alanswx/Arcade-MCR2-TangFPGA/docs/for_mitch_2026-08-27.md

# Shield PCB — summary for Mitch, 2026-08-27

Thanks for the quick turnaround on the 08-25 review. Here is where the board
stands after your 08-27 upload (`9fb5ccc` / `22d051d`), checked the same way
as before: your committed `MCR_prototype_PCB.net` (135 parts, all 12 sheets)
now matches an independently generated netlist exactly, and both match the
`.kicad_pcb` pad-for-pad — 185 nets, zero differences. DRC is clean (0
unconnected, 0 violations). So the gerbers are the schematic; the remaining
questions are all design, not tooling.

## Fixed — thank you

| | |
|---|---|
| U1/U2 CLK ↔ LOAD swap | all six '165s consistent now |
| ESD arrays in series with caps | SRV05s on the input nodes; dropping the 32 caps is fine |
| 1N4148W feeding the console | 1N5822 on a 1.0 mm trace — good |
| decoupling | 16 × 100 nF + 2 × 100 µF; both rails covered |
| THS7374 | BYPASS on JP4, 75 Ω series on all five outputs |
| J5 | grounds on 9/18, meter across +12 V and the ULN, `Out_Clear` pulled up |

## Please fix before ordering

**1. ADS7830 logic levels (two nets).** VDD and REF are now both +5 V, which
fixes the REF-above-VDD problem but creates another: the FPGA's I²C is 3.3 V
and the ADS7830's VIH is 0.7 × VDD = 3.5 V at 5 V, so SCL/SDA highs are out
of spec. Go the other way: **VDD = +3.3 V**, leave REF as an output with
100 nF to ground (internal 2.5 V reference), and put the volume pot across
+3.3 V so the wiper stays in range.

**2. Mounting holes.** There are none — the only 3.2 mm drills are the DE-15
bracket pair, and the 1.6 mm pair is D4's leads. A 267 × 199 mm 4-layer board
with a 40-pin socket and eight MTA headers needs standoffs; four corner holes
at least.

## Worth doing on this spin (they will show up on first hookup)

**3. THS7374 input level.** The 510/1k/2k ladder still feeds the amp input
with no shunt, so full-scale is 3.3 V, doubled to 6.6 V against a ~2.3 V
linear input range — the top of the range clips. A **75 Ω to ground at each
of U13's three inputs** brings full-scale to ~0.7 V, which is what the 2×
gain and the 75 Ω series resistor are designed around. Also note the VGA
connector and J2 hang off the *same* 75 Ω, so with both plugged in the level
halves; separate resistors per connector if both stay.

**4. Audio.** The board has no amplifier. On the real cabinet, J3 pins 7/9
(and DoT's 6/7 and 9/10) are the *speaker terminals* of the sound board's own
amp — a cabinet speaker plugged into this J3 gets a 2 kΩ-source line-level
signal and will be near-silent. Either add an LM386/TPA-class stage per
channel (the spec assumed one on the 12 V rail) or document that an external
amp is required.

On the Discs of Tron 10-pin J3: per the archived pinout, 6/7 are the + and −
of speaker 1 and 9/10 of speaker 2. The board puts `AUD_PWM_R1` on 6 and
`AUD_PWM_L1` on 7 — two different channels across one speaker. DoT has two
speakers, each bridge-driven, not four. If you want the second pair
(`AUD_PWM_L2/R2` on J10 pins 1 and 5) to survive, it needs an RTL decision
on our side too — nothing generates a second stereo pair today, and those
balls currently carry video bit 0.

## Small / for the record

- No cap on the regulator side of L1/L2 (U24/U25 IN nets are just inductor +
  module pin). RECOM wants the input cap at the pin; 10 µF after each
  inductor.
- No I²C pull-ups on `ADC_SDA/SCL`. FPGA internal pull-ups will do for the
  prototype.
- `Start 1/2/3 Lamp` nets on U10 go to no connector (ERC flags them).
- J5.20/21 meter polarity is the reverse of the table (20 = Return, 21 =
  Meter 1). Harmless for a bare coil; check how the harness uses "Return".
- **J1 pin 18 = +12 V and 6/7/10/20 = GND: I could not verify these positions**
  — the archived table lists J1's functions but not its 20 pin numbers.
  Please check against the MCR power-supply manual; a wrong +12 V pin on the
  .156" connector is the one mistake that destroys parts.
- J0 (the 2×20 socket) is top-side at (125, 148). Just confirm the stacking
  and that pin 1 lands on J10 pin 1.

## Agreed / recorded on our side

- Pin 9 = service switch, pin 11 = console +5 V through D4, pins 19/20/29/30
  = ADC, pins 1/5 = second audio pair — all now in `docs/shield_j10_pinout.md`
  as built.
- RTL to-do list (I²C master, `OUT_CLEAR_N` high, second audio pair or
  retire video bit 0) is in `TODO.md` under "Shield PCB".
- Full detail with the per-item table: `docs/pcb_review_2026-08-25.md`.

---

## 2026-08-28 follow-up

Checked `d5f0787` the same way: your `.net` (143 parts), my independent
netlist and the board agree pad-for-pad (186 nets), DRC clean.

Everything I asked for is in: ADS7830 on 3.3 V with the REF cap and the pot
on 3.3 V, 1 k I²C pull-ups, 75 Ω shunts on the THS7374 inputs, 10 µF after
L1/L2, five M4 mounting holes. **From my side there is nothing left to hold
the order for.**

**Audio — you're right and I was wrong.** I had read J3's "o+/o−" as the
sound board's own speaker terminals. With the external dual-amplifier PCB
in the cabinet, line level on J3 is correct and no on-board amp is needed,
and with DoT Environmental driving four speakers independently, J3_DOT1
6/7/9/10 as four channels is the right assignment. I've withdrawn that
item. What remains from it is on our side: the FPGA doesn't generate a
second stereo pair yet, so J10 pins 1/5 will carry video bit 0 until the RTL
is updated — harmless into your RC filter.

Two small things, neither a blocker: VGA and J2 share one 75 Ω per channel,
so the level halves if both are plugged in at once; and the three start-lamp
nets on U10 still go to no connector.

The one thing I still can't check myself: **J1 pin 18 = +12 V and 6/7/10/20 =
GND** — please confirm the .156" positions against the manual before power
is applied.
