alanswx/Arcade-MCR2-TangFPGA/docs/MCR_Master_Pinouts.pdf

# Ultimate MCR Master Pinout Matrix

Connector-Pin | Standard MCR Function | Solar Fox (MCR-1) | Kick / Kickman (MCR-1) | Tron (MCR-2) | Satan's Hollow (MCR-2) | Kozmik Krooz'r (MCR-2) | Wacko (MCR-2) | Domino Man (MCR-2) | Tapper (MCR-3) | Journey (MCR-3) | Timber (MCR-3) | Discs of Tron (MCR-3) | Spy Hunter (MCR-3) | Crater Raider (MCR-3)
J2-1 | P1 Up | P1 Up | N/C | P1 Up | P1 Left | N/C | P1 Up | P1 Up | P1 Up | P1 Up | P1 Up | P1 Up | Machine Gun | N/C
J2-2 | P1 Down | P1 Down | N/C | P1 Down | P1 Right | N/C | P1 Down | P1 Down | P1 Down | P1 Down | P1 Down | P1 Down | Missiles | N/C
J2-3 | P1 Left | P1 Left | N/C | P1 Left | N/C | N/C | P1 Left | P1 Left | P1 Left | P1 Left | P1 Left | P1 Left | Oil Slick | P1 Left
J2-4 | P1 Right | P1 Right | N/C | P1 Right | N/C | N/C | P1 Right | P1 Right | P1 Right | P1 Right | P1 Right | P1 Right | Smoke Screen | P1 Right
J2-5 | P1 Button 1 | Fire / Turbo | Kick | Fire (Trigger) | Fire (Trigger) | Fire | N/C | Place / Strike | Pour / Serve | Fire | N/C | Fire (Trigger) | Weapons Van | Fire
J2-6 | P1 Button 2 | N/C | Catch | N/C | Shield | N/C | N/C | N/C | N/C | N/C | N/C | Deflect | N/C | Shield
J2-13 | Ground | Ground | Ground | Ground | Ground | Ground | Ground | Ground | Ground | Ground | Ground | Ground | Ground | Ground
J5-1 | P2 Mux / Data Bit 0 (Opt Y) | No J5 | No J5 | No J5 | No J5 | No J5 | Trackball Y-Axis (D0) | No J5 | N/C | N/C | N/C | N/C | N/C | N/C
J5-2 | P2 Mux / Data Bit 1 (Opt Y) | No J5 | No J5 | No J5 | No J5 | No J5 | Trackball Y-Axis (D1) | No J5 | N/C | N/C | N/C | N/C | N/C | N/C
J5-3 | P2 Mux / Data Bit 2 (Opt Y) | No J5 | No J5 | No J5 | No J5 | No J5 | Trackball Y-Axis (D2) | No J5 | N/C | N/C | N/C | N/C | N/C | N/C
J5-4 | P2 Mux / Data Bit 3 (Opt Y) | No J5 | No J5 | No J5 | No J5 | No J5 | Trackball Y-Axis (D3) | No J5 | N/C | N/C | N/C | N/C | N/C | N/C
J5-5 | P2 Mux / Data Bit 4 (Opt Y) | No J5 | No J5 | No J5 | No J5 | No J5 | Trackball Y-Axis (D4) | No J5 | N/C | N/C | N/C | N/C | N/C | N/C
J5-6 | P2 Mux / Data Bit 5 (Opt Y) | No J5 | No J5 | No J5 | No J5 | No J5 | Trackball Y-Axis (D5) | No J5 | N/C | N/C | N/C | N/C | N/C | N/C
J5-15 | P2 Up / Data Bit 6 (Opt Y) | No J5 | No J5 | No J5 | No J5 | No J5 | Trackball Y-Axis (D6) | No J5 | P2 Up | N/C | P2 Up | Aim Up | N/C | N/C
J5-16 | P2 Down / Data Bit 7 (Opt Y) | No J5 | No J5 | No J5 | No J5 | No J5 | Trackball Y-Axis (D7) | No J5 | P2 Down | N/C | P2 Down | Aim Down | N/C | N/C
J5-17 | P2 Left | No J5 | No J5 | No J5 | No J5 | No J5 | N/C | No J5 | P2 Left | N/C | P2 Left | N/C | N/C | N/C
J5-18 | P2 Right | No J5 | No J5 | No J5 | No J5 | No J5 | N/C | No J5 | P2 Right | N/C | P2 Right | N/C | N/C | N/C
J5-19 | P2 Button 1 | No J5 | No J5 | No J5 | No J5 | No J5 | N/C | No J5 | P2 Pour | N/C | N/C | N/C | N/C | N/C
J3-1 | Coin 1 | Coin 1 | Coin 1 | Coin 1 | Coin 1 | Coin 1 | Coin 1 | Coin 1 | Coin 1 | Coin 1 | Coin 1 | Coin 1 | Coin 1 | Coin 1
J3-2 | Coin 2 | Coin 2 | Coin 2 | Coin 2 | Coin 2 | Coin 2 | Coin 2 | Coin 2 | Coin 2 | Coin 2 | Coin 2 | Coin 2 | Coin 2 | Coin 2
J3-3 | Start 1 | Start 1 | Start 1 | Start 1 | Start 1 | Start 1 | Start 1 | Start 1 | Start 1 | Start 1 | Start 1 | Start 1 | Start 1 | Start 1
J3-4 | Start 2 | Start 2 | Start 2 | Start 2 | Start 2 | Start 2 | Start 2 | Start 2 | Start 2 | Start 2 | Start 2 | Start 2 | N/C | Start 2
J3-5 | Tilt | Tilt | Tilt | Tilt | Tilt | Tilt | Tilt | Tilt | Tilt | Tilt | Tilt | Tilt | Tilt | Tilt
J4-1 | Data Bit 0 (Opt X) | Data Bit 0 | Spinner X (D0) | Opt/Main (D0) | Data Bit 0 | Spinner X (D0) | Trackball X-Axis (D0) | Data Bit 0 | Data Bit 0 | Data Bit 0 | Data Bit 0 | Rotary (D0) | Steer/Gas (D0) | Data Bit 0
J4-2 | Data Bit 1 (Opt X) | Data Bit 1 | Spinner X (D1) | Opt/Main (D1) | Data Bit 1 | Spinner X (D1) | Trackball X-Axis (D1) | Data Bit 1 | Data Bit 1 | Data Bit 1 | Data Bit 1 | Rotary (D1) | Steer/Gas (D1) | Data Bit 1
J4-3 | Data Bit 2 (Opt X) | Data Bit 2 | Spinner X (D2) | Opt/Main (D2) | Data Bit 2 | Spinner X (D2) | Trackball X-Axis (D2) | Data Bit 2 | Data Bit 2 | Data Bit 2 | Data Bit 2 | Rotary (D2) | Steer/Gas (D2) | Data Bit 2
J4-4 | Data Bit 3 (Opt X) | Data Bit 3 | Spinner X (D3) | Opt/Main (D3) | Data Bit 3 | Spinner X (D3) | Trackball X-Axis (D3) | Data Bit 3 | Data Bit 3 | Data Bit 3 | Data Bit 3 | Rotary (D3) | Steer/Gas (D3) | Data Bit 3
J4-5 | Data Bit 4 (Opt X) | Data Bit 4 | Spinner X (D4) | Opt/Main (D4) | Data Bit 4 | Spinner X (D4) | Trackball X-Axis (D4) | Data Bit 4 | Data Bit 4 | Data Bit 4 | Data Bit 4 | Rotary (D4) | Steer/Gas (D4) | Data Bit 4
J4-6 | Data Bit 5 (Opt X) | Data Bit 5 | Spinner X (D5) | Opt/Main (D5) | Data Bit 5 | Spinner X (D5) | Trackball X-Axis (D5) | Data Bit 5 | Data Bit 5 | Data Bit 5 | Data Bit 5 | Rotary (D5) | Steer/Gas (D5) | Data Bit 5
J4-7 | Data Bit 6 (Opt X) | Data Bit 6 | Spinner X (D6) | Opt/Main (D6) | Data Bit 6 | Spinner X (D6) | Trackball X-Axis (D6) | Data Bit 6 | Data Bit 6 | Data Bit 6 | Data Bit 6 | Rotary (D6) | Steer/Gas (D6) | Data Bit 6
J4-8 | Key | Key | Key | Key | Key | Key | Key | Key | Key | Key | Key | Key | Key | Key
J4-9 | Data Bit 7 (Opt X) | Data Bit 7 | Spinner X (D7) | Opt/Main (D7) | Data Bit 7 | Spinner X (D7) | Trackball X-Axis (D7) | Data Bit 7 | Data Bit 7 | Data Bit 7 | Data Bit 7 | Rotary (D7) | Steer/Gas (D7) | Data Bit 7
J4-10 | Ground | Ground | Ground | Ground | Ground | Ground | Ground | Ground | Ground | Ground | Ground | Ground | Ground | Ground
Video - Pin 1 | Red | Red | Red | Red | Red | Red | Red | Red | Red | Red | Red | Red | Red | Red
Video - Pin 2 | Video GND | Video GND | Video GND | Video GND | Video GND | Video GND | Video GND | Video GND | Video GND | Video GND | Video GND | Video GND | Video GND | Video GND
Video - Pin 3 | Green | Green | Green | Green | Green | Green | Green | Green | Green | Green | Green | Green | Green | Green
Video - Pin 4 | Video GND | Video GND | Video GND | Video GND | Video GND | Video GND | Video GND | Video GND | Video GND | Video GND | Video GND | Video GND | Video GND | Video GND

Connector-Pin | Standard MCR Function | Solar Fox (MCR-1) | Kick / Kickman (MCR-1) | Tron (MCR-2) | Satan's Hollow (MCR-2) | Kozmik Krooz'r (MCR-2) | Wacko (MCR-2) | Domino Man (MCR-2) | Tapper (MCR-3) | Journey (MCR-3) | Timber (MCR-3) | Discs of Tron (MCR-3) | Spy Hunter (MCR-3) | Crater Raider (MCR-3)
Video - Pin 5 | Blue | Blue | Blue | Blue | Blue | Blue | Blue | Blue | Blue | Blue | Blue | Blue | Blue | Blue
Video - Pin 6 | Video GND | Video GND | Video GND | Video GND | Video GND | Video GND | Video GND | Video GND | Video GND | Video GND | Video GND | Video GND | Video GND | Video GND
Video - Pin 7 | Key | Key | Key | Key | Key | Key | Key | Key | Key | Key | Key | Key | Key | Key
Video - Pin 8 | H-Sync (-) | H-Sync (-) | H-Sync (-) | H-Sync (-) | H-Sync (-) | H-Sync (-) | H-Sync (-) | H-Sync (-) | H-Sync (-) | H-Sync (-) | H-Sync (-) | H-Sync (-) | H-Sync (-) | H-Sync (-)
Video - Pin 9 | V-Sync (-) | V-Sync (-) | V-Sync (-) | V-Sync (-) | V-Sync (-) | V-Sync (-) | V-Sync (-) | V-Sync (-) | V-Sync (-) | V-Sync (-) | V-Sync (-) | V-Sync (-) | V-Sync (-) | V-Sync (-)
