alanswx/Arcade-MCR2-TangFPGA/src/rtl/steering_control.vhd

-- Vendored 2026-07-30 from refs/Arcade-MCR3Scroll_MiSTer/rtl/steering_control.vhd
-- (MiSTer Arcade-MCR3Scroll). Unmodified. Absolute-position wheel/pedal
-- decoder simulation for Spy Hunter and Turbo Tag; lives in the TOP, not the
-- core, exactly as upstream has it.
library ieee;
use ieee.std_logic_1164.all;
use ieee.std_logic_unsigned.all;
use ieee.numeric_std.all;

entity steering_control is
generic (
	steering_min   : std_logic_vector(7 downto 0) := x"34";
	steering_max   : std_logic_vector(7 downto 0) := x"B4";
	steering_mid   : std_logic_vector(7 downto 0) := x"74";
	steering_step  : std_logic_vector(7 downto 0) := x"08";
	gas_min        : std_logic_vector(8 downto 0) := '0'&x"30";
	gas_max        : std_logic_vector(8 downto 0) := '0'&x"FF";
	gas_step       : std_logic_vector(8 downto 0) := '0'&x"08";
	gas_reverse    : std_logic := '0'
);
port(
	clk            : in  std_logic;
	reset          : in  std_logic;
	vsync          : in  std_logic;

	gas_plus       : in  std_logic;
	gas_minus      : in  std_logic;
	steering_plus  : in  std_logic;
	steering_minus : in  std_logic;
	steering       : out std_logic_vector(7 downto 0);
	gas            : out std_logic_vector(7 downto 0)
);
end steering_control;

architecture struct of steering_control is
	signal steering_r       : std_logic_vector(7 downto 0);
	signal steering_next    : std_logic_vector(7 downto 0);
	signal steering_plus_r  : std_logic;
	signal steering_minus_r : std_logic;
	signal steering_timer   : std_logic_vector(5 downto 0);

	signal gas_r            : std_logic_vector(8 downto 0);
	signal gas_next         : std_logic_vector(8 downto 0);
	signal gas_plus_r       : std_logic;
	signal gas_minus_r      : std_logic;
	signal gas_timer        : std_logic_vector(5 downto 0);

	signal vsync_r          : std_logic;
begin

-- absolute position decoder simulation
--
--  steering :
--       thresholds        median
--   F5 <  left 8   < 34    30
--   35 <  left 7   < 3C    38
--   3D <  left 6   < 44    40
--   45 <  left 5   < 4C    48     
--   4D <  left 4   < 54    50
--   45 <  left 3   < 5C    58
--   5D <  left 2   < 64    60
--   65 <  left 1   < 6C    68
--   6D < centrered < 74    70
--   75 <  right 1  < 7C    78
--   7D <  right 2  < 84    80
--   85 <  right 3  < 8C    88
--   8D <  right 4  < 94    90
--   95 <  right 5  < 9C    98
--   9D <  right 6  < A4    A0
--   A5 <  right 7  < AC    A8
--   AD <  right 8  < F4    BO

-- gas :
--         threshold          median
--    00 < gas pedal 00 < 3B   (39)  3E-5
--    3C < gas pedal 01 < 40    3E
--    41 < gas pedal 02 < 45    43
--    46 < gas pedal 03 < 4A    48      
--    4B < gas pedal 04 < 4F    4D
--    50 < gas pedal 05 < 54    52
--    55 < gas pedal 06 < 59    57
--    5A < gas pedal 07 < 5E    5C
--    5F < gas pedal 08 < 63    61
--     ...
--    FA < gas pedal 27 < FE    FC
--    FF = gas pedal 28        (FF)  FC+4


gas <= gas_r(7 downto 0);
gas_next <= gas_r - gas_step when gas_plus  = '1' and gas_reverse = '1' else
            gas_r + gas_step when gas_minus = '1' and gas_reverse = '1' else
            gas_r + gas_step when gas_plus  = '1' and gas_reverse = '0' else
            gas_r - gas_step when gas_minus = '1' and gas_reverse = '0' else
            gas_r;

steering <= steering_r;
steering_next <= steering_r + steering_step when steering_plus = '1' else steering_r - steering_step;

process (clk, reset)
begin
	if reset = '1' then
		if gas_reverse = '1' then
			gas_r <= gas_max;
		else
			gas_r <= gas_min;
		end if;
		steering_r <= steering_mid;
	else

		if rising_edge(clk) then
			gas_plus_r       <= gas_plus;
			gas_minus_r      <= gas_minus;
			steering_plus_r  <= steering_plus;
			steering_minus_r <= steering_minus;
			vsync_r          <= vsync;
			
			-- gas increase/decrease as long as btn is pushed
			-- keep current value when no btn is pushed
			if (gas_plus_r = not gas_plus)  or (gas_minus_r = not gas_minus) then
				gas_timer <= (others => '0');
			else
				if vsync_r ='0' and vsync = '1' then 
					if (gas_timer >= 5 and (gas_minus_r = '1' or gas_plus_r = '1')) then --tune inc/dec rate
						gas_timer <= (others => '0');
					else
						gas_timer <= gas_timer + 1;
					end if;
				end if;
			end if;

			if vsync_r ='0' and vsync = '1' and gas_timer = 0 then	
				gas_r <= gas_next;
				if gas_next < gas_min then
					gas_r <= gas_min;
				elsif gas_next > gas_max then
					gas_r <= gas_max;
				end if;
			end if;

			-- steering increase/decrease as long as btn is pushed
			-- return to center value when no btn is pushed
			if (steering_plus_r = not steering_plus)  or (steering_minus_r = not steering_minus) then
				steering_timer <= (others => '0');
			else
				if vsync_r ='0' and vsync = '1' then 
					if (steering_timer >= 7 and (steering_minus_r = '1' or  steering_plus_r = '1')) or   -- tune btn pushed   rate
						(steering_timer >= 3 and (steering_minus_r = '0' and steering_plus_r = '0')) then -- tune btn released rate
						steering_timer <= (others => '0');
					else
						steering_timer <= steering_timer + 1;
					end if;
				end if;
			end if;
			
			if vsync_r ='0' and vsync = '1' and steering_timer = 0 then	
				if steering_plus = '1' then 
					if steering_next > steering_max then steering_r <= steering_max; else steering_r <= steering_next; end if;
				elsif steering_minus = '1' then
					if steering_next < steering_min then steering_r <= steering_min; else steering_r <= steering_next; end if;
				else
					if steering_r < steering_mid - steering_step then steering_r <= steering_r + steering_step; end if;						
					if steering_r > steering_mid + steering_step then steering_r <= steering_r - steering_step; end if;
					if (steering_r >= steering_mid - steering_step) and (steering_r <= steering_mid + steering_step) then steering_r <= steering_mid; end if;						
				end if;
			end if;
		end if;
	end if;
end process;	

end struct;
