alanswx/Arcade-MCR2-TangFPGA/src/rtl/sdram_gw.sv

// sdram_gw.sv - Gowin adaptation of the MiSTer Arcade-MCR3 multi-port
// SDRAM controller (refs/Arcade-MCR3_MiSTer/rtl/sdram.sv), vendored 2026-07.
// Only change from upstream: module renamed and the Altera altddio_out
// SDRAM_CLK forwarder replaced with a Gowin ODDR (see below). This is the
// controller MCR-3 will use; the SDRAM memtest exercises it so the physical
// module + pins + clock phase are validated before a core rides on it.
// Runs at ~100 MHz (refresh RFRSH_CYCLES sized for that).
//
// sdram.v
//
// sdram controller implementation for the MiST board
// https://github.com/mist-devel/mist-board
// 
// Copyright (c) 2013 Till Harbaum <till@harbaum.org> 
// Copyright (c) 2019 Gyorgy Szombathelyi
//
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

module sdram_gw #(
	// Cycles between auto-refreshes. Default 842 suits the memtest's 100 MHz
	// clock; the MCR-3 build runs at 80 MHz and overrides to 600 (7.5us < the
	// 7.81us tREF row interval). Sized per SDRAM clock so data is retained.
	parameter [9:0] RFRSH_CYCLES = 10'd842,
	// RAS-only refresh (2026-07-24): measured on the Tang SDRAM module, the
	// array decays to all-FF in ~26s with NO access while AUTO_REFRESH issues
	// at the correct ~133k/s - commands sent but ineffective. AUTO_REFRESH is
	// the only command asserting nRAS and nCAS low together; reads/writes
	// (proven-good patterns) never do. This mode refreshes via explicit
	// ACTIVE(bank,row) + PRECHARGE-ALL instead. Needs 4x the command rate
	// (per-bank rows): set RFRSH_CYCLES ~150 at 80MHz.
	parameter       RAS_REFRESH  = 1'b0
) (

	// interface to the MT48LC16M16 chip
	inout      [15:0] SDRAM_DQ,   // 16 bit bidirectional data bus (Gowin: driven via the tristate assign below)
	output reg [12:0] SDRAM_A,    // 13 bit multiplexed address bus
	output            SDRAM_DQML, // two byte masks (continuously assigned)
	output            SDRAM_DQMH, // two byte masks
	output reg [1:0]  SDRAM_BA,   // two banks
	output            SDRAM_nCS,  // a single chip select
	output            SDRAM_nWE,  // write enable
	output            SDRAM_nRAS, // row address select
	output            SDRAM_nCAS, // columns address select
	output            SDRAM_CKE,
	output            SDRAM_CLK, 
	
	// cpu/chipset interface
	input             init_n,     // init signal after FPGA config to initialize RAM
	input             clk,        // sdram clock
	// Optional phase-shifted copy of clk for the SDRAM_CLK pin forwarder
	// (see the ODDR at the bottom). Tie to clk when no shift is wanted.
	input             clk_fwd,

	input             port1_req,
	output reg        port1_ack,
	input             port1_we,
	input      [23:1] port1_a,
	input       [1:0] port1_ds,
	input      [15:0] port1_d,
	output reg [15:0] port1_q,

	input      [23:1] cpu1_addr,
	output reg [15:0] cpu1_q,
	input      [23:1] cpu2_addr,
	output reg [15:0] cpu2_q,
	input      [23:1] cpu3_addr,
	output reg [15:0] cpu3_q,

	input             port2_req,
	output reg        port2_ack,
	input             port2_we,
	input      [23:1] port2_a,
	input       [1:0] port2_ds,
	input      [15:0] port2_d,
	output reg [31:0] port2_q,
	
	input      [23:2] sp_addr,
	output reg [31:0] sp_q,

	// DIAGNOSTIC (temporary): counts AUTO_REFRESH commands actually issued.
	// At 80 MHz / RFRSH_CYCLES=600 expect ~133k/s (wraps ~3x/s). Frozen at 0
	// means the refresh branch never fires. Leave unconnected when unused.
	// 24-bit: at the intended ~133k/s a 16-bit counter wraps ~4x between
	// beacon samples, which made the rate unmeasurable (and produced the
	// bogus "2.3k/s starvation" reading). The top displays bits [23:8].
	output reg [23:0] dbg_refresh = 24'd0,
	// DIAGNOSTIC: refresh-demand cycles lost to each blocker (RAS1 slots where
	// need_refresh was pending): blk1 = bank2/3 port busy, blk0 = port[0]
	// we/oe_latch gate. Whichever runs ~130k/s is what starves refresh.
	output reg [15:0] dbg_blk0 = 16'd0,
	output reg [15:0] dbg_blk1 = 16'd0
);

assign SDRAM_CKE = 1;
assign SDRAM_nCS = 0;
assign { SDRAM_DQMH, SDRAM_DQML } = SDRAM_A[12:11];

// Gowin bidirectional DQ: MiSTer drove `inout reg SDRAM_DQ` procedurally,
// which Gowin rejects (EX3900). Model the tristate explicitly instead.
reg  [15:0] sd_dq_out;
reg         sd_dq_oe;
assign SDRAM_DQ = sd_dq_oe ? sd_dq_out : 16'bZ;

localparam RASCAS_DELAY   = 3'd2;   // tRCD=20ns -> 2 cycles@<100MHz
localparam BURST_LENGTH   = 3'b001; // 000=1, 001=2, 010=4, 011=8
localparam ACCESS_TYPE    = 1'b0;   // 0=sequential, 1=interleaved
localparam CAS_LATENCY    = 3'd2;   // CL2, as nand2mario runs this module
localparam OP_MODE        = 2'b00;  // only 00 (standard operation) allowed
localparam NO_WRITE_BURST = 1'b1;   // 0= write burst enabled, 1=only single access write

localparam MODE = { 3'b000, NO_WRITE_BURST, OP_MODE, CAS_LATENCY, ACCESS_TYPE, BURST_LENGTH}; 

// 64ms/8192 rows = 7.8us -> 842 cycles@108MHz
// RFRSH_CYCLES is now a module parameter (see the header) so the 80 MHz MCR-3
// build can shrink it; the memtest leaves it at the 842 default.

// ---------------------------------------------------------------------
// ------------------------ cycle state machine ------------------------
// ---------------------------------------------------------------------

/*
 SDRAM state machine for 2 bank interleaved access
 1 word burst, CL2
cmd issued  registered
 0 RAS0     
 1          ras0, data1 returned
 2 CAS0     data1 returned
 3 RAS1     cas0
 4          ras1
 5 CAS1     data0 returned
 6          cas1, data0 returned (discarded)
 
*/

localparam STATE_FIRST     = 3'd0;   // first state in cycle
localparam STATE_RAS0      = 3'd0;
localparam STATE_RAS1      = 3'd3;   // Second ACTIVE command after RAS0 + tRRD (15ns)
localparam STATE_CAS0      = STATE_RAS0 + RASCAS_DELAY; // CAS phase - 2
localparam STATE_CAS1      = STATE_RAS1 + RASCAS_DELAY; // CAS phase - 5
localparam STATE_READ1     = 3'd2;   // upstream value (moving these past
localparam STATE_READ1b    = 3'd3;   // RAS1 breaks oe_latch clearing - use
                                     // CAP_DELAY on the data path instead)
localparam STATE_READ0     = 3'd6;
localparam STATE_LAST      = 3'd6;

reg [2:0] t;
always @(posedge clk) begin
	t <= t + 1'd1;
	if (t == STATE_LAST) t <= STATE_FIRST;
end

// ---------------------------------------------------------------------
// --------------------------- startup/reset ---------------------------
// ---------------------------------------------------------------------

// wait 1ms (32 8Mhz cycles) after FPGA config is done before going
// into normal operation. Initialize the ram in the last 16 reset cycles (cycles 15-0)
reg [4:0]  reset;
reg        init = 1'b1;
always @(posedge clk, negedge init_n) begin
	if(!init_n) begin
		reset <= 5'h1f;
		init <= 1'b1;
	end else begin
		if((t == STATE_LAST) && (reset != 0)) reset <= reset - 5'd1;
		init <= !(reset == 0);
	end
end

// ---------------------------------------------------------------------
// ------------------ generate ram control signals ---------------------
// ---------------------------------------------------------------------

// all possible commands
localparam CMD_NOP             = 3'b111;
localparam CMD_ACTIVE          = 3'b011;
localparam CMD_READ            = 3'b101;
localparam CMD_WRITE           = 3'b100;
localparam CMD_BURST_TERMINATE = 3'b110;
localparam CMD_PRECHARGE       = 3'b010;
localparam CMD_AUTO_REFRESH    = 3'b001;
localparam CMD_LOAD_MODE       = 3'b000;

reg [2:0]  sd_cmd;   // current command sent to sd ram
reg [15:0] sd_din;
reg [15:0] sp_q_lo;  // first burst beat of an sp read, committed at READ1b
// drive control signals according to current command
assign SDRAM_nRAS = sd_cmd[2];
assign SDRAM_nCAS = sd_cmd[1];
assign SDRAM_nWE  = sd_cmd[0];

reg [23:1] addr_latch[3];
reg [23:1] addr_latch_next[2];
reg [23:1] addr_last[4];
reg [23:2] addr_last2[2];
reg [15:0] din_latch[2];
reg  [1:0] oe_latch;
reg  [1:0] we_latch;
reg  [1:0] ds[2];

reg        port1_state;
reg        port2_state;

localparam PORT_NONE  = 3'd0;
localparam PORT_CPU1  = 3'd1;
localparam PORT_CPU2  = 3'd2;
localparam PORT_CPU3  = 3'd3;
localparam PORT_SP    = 3'd1;
localparam PORT_REQ   = 3'd4;

reg  [2:0] next_port[2];
reg  [2:0] port[2];

reg        refresh;
reg [10:0] refresh_cnt;
reg        need_refresh;
reg [14:0] ref_cnt   = 15'd0;   // RAS_REFRESH: {row[12:0], bank[1:0]}
reg        ref_phase = 1'b0;    // RAS_REFRESH: row open, precharge next slot

// PORT1: bank 0,1
always @(*) begin
	if (refresh) begin
		next_port[0] = PORT_NONE;
		addr_latch_next[0] = addr_latch[0];
	end else if (port1_req ^ port1_state) begin
		next_port[0] = PORT_REQ;
		addr_latch_next[0] = port1_a;
	end else if (cpu1_addr != addr_last[PORT_CPU1]) begin
		next_port[0] = PORT_CPU1;
		addr_latch_next[0] = cpu1_addr;
	end else if (cpu2_addr != addr_last[PORT_CPU2]) begin
		next_port[0] = PORT_CPU2;
		addr_latch_next[0] = cpu2_addr;
	end else if (cpu3_addr != addr_last[PORT_CPU3]) begin
		next_port[0] = PORT_CPU3;
		addr_latch_next[0] = cpu3_addr;
	end else begin
		next_port[0] = PORT_NONE;
		addr_latch_next[0] = addr_latch[0];
	end
end

// PORT1: bank 2,3
always @(*) begin
	if (port2_req ^ port2_state) begin
		next_port[1] = PORT_REQ;
		addr_latch_next[1] = port2_a;
	end else if (sp_addr != addr_last2[PORT_SP]) begin
		next_port[1] = PORT_SP;
		addr_latch_next[1] = { sp_addr, 1'b0 };
	end else begin
		next_port[1] = PORT_NONE;
		addr_latch_next[1] = addr_latch[1];
	end
end

always @(posedge clk) begin

	// permanently latch ram data to reduce delays
	sd_din <= SDRAM_DQ;
	sd_dq_oe <= 1'b0;   // release the bus (Gowin tristate)
	sd_cmd <= CMD_NOP;  // default: idle
	if(~&refresh_cnt) refresh_cnt <= refresh_cnt + 1'd1;
	need_refresh <= (refresh_cnt >= RFRSH_CYCLES);

	if(init) begin
		// initialization takes place at the end of the reset phase
		if(t == STATE_FIRST) begin

			if(reset == 15) begin
				sd_cmd <= CMD_PRECHARGE;
				SDRAM_A[10] <= 1'b1;      // precharge all banks
			end

			if(reset == 10 || reset == 8) begin
				sd_cmd <= CMD_AUTO_REFRESH;
			end

			if(reset == 2) begin
				sd_cmd <= CMD_LOAD_MODE;
				SDRAM_A <= MODE;
				SDRAM_BA <= 2'b00;
			end
		end
	end else begin
		// RAS phase
		// bank 0,1
		if(t == STATE_RAS0) begin
			addr_latch[0] <= addr_latch_next[0];
			port[0] <= next_port[0];
			{ oe_latch[0], we_latch[0] } <= 2'b00;

			if (next_port[0] != PORT_NONE) begin
				sd_cmd <= CMD_ACTIVE;
				SDRAM_A <= addr_latch_next[0][22:10];
				SDRAM_BA <= {1'b0, addr_latch_next[0][23]};
				addr_last[next_port[0]] <= addr_latch_next[0];
				if (next_port[0] == PORT_REQ) begin
					{ oe_latch[0], we_latch[0] } <= { ~port1_we, port1_we };
					ds[0] <= port1_ds;
					din_latch[0] <= port1_d;
					port1_state <= port1_req;
				end else begin
					{ oe_latch[0], we_latch[0] } <= 2'b10;
					ds[0] <= 2'b11;
				end
			end
		end

		// bank 2,3
		if(t == STATE_RAS1) begin
			refresh <= 1'b0;
			addr_latch[1] <= addr_latch_next[1];
			{ oe_latch[1], we_latch[1] } <= 2'b00;
			port[1] <= next_port[1];

			if (RAS_REFRESH && ref_phase) begin
				// close the refresh row opened last frame (RAS1->RAS1 = 7 cycles
				// = 87.5ns >= tRAS). Nothing else is open: port0 idle, port1/2
				// bursts auto-precharge. Pending port work waits one frame.
				sd_cmd <= CMD_PRECHARGE;
				SDRAM_A[10] <= 1'b1;
				ref_phase <= 1'b0;
				port[1] <= PORT_NONE;   // don't launch work this slot
			end
			else if (next_port[1] != PORT_NONE) begin
				if (need_refresh) dbg_blk1 <= dbg_blk1 + 1'd1;
				sd_cmd <= CMD_ACTIVE;
				SDRAM_A <= addr_latch_next[1][22:10];
				SDRAM_BA <= {1'b1, addr_latch_next[1][23]};
				addr_last2[next_port[1]] <= addr_latch_next[1][23:2];
				if (next_port[1] == PORT_REQ) begin
					// NOTE: this is the port2 (bank 2,3) path - it must gate on
					// port2_we, not port1_we. The original had port1_we here (a
					// copy-paste from the bank 0,1 block); harmless until port2
					// is actually used for writes (MCR-3 sprite load), where it
					// made every port2 write silently decode as a read.
					{ oe_latch[1], we_latch[1] } <= { ~port2_we, port2_we };
					ds[1] <= port2_ds;
					din_latch[1] <= port2_d;
					port2_state <= port2_req;
				end else begin
					{ oe_latch[1], we_latch[1] } <= 2'b10;
					ds[1] <= 2'b11;
				end
			end
			else if (need_refresh && !we_latch[0] && !oe_latch[0]) begin
				refresh <= 1'b1;
				refresh_cnt <= 0;
				dbg_refresh <= dbg_refresh + 1'd1;
				if (RAS_REFRESH) begin
					sd_cmd    <= CMD_ACTIVE;
					SDRAM_BA  <= ref_cnt[1:0];
					SDRAM_A   <= ref_cnt[14:2];
					ref_cnt   <= ref_cnt + 15'd1;
					ref_phase <= 1'b1;
				end else begin
					sd_cmd <= CMD_AUTO_REFRESH;
				end
			end
			else if (need_refresh) begin
				dbg_blk0 <= dbg_blk0 + 1'd1;
			end
		end

		// CAS phase
		if(t == STATE_CAS0 && (we_latch[0] || oe_latch[0])) begin
			sd_cmd <= we_latch[0]?CMD_WRITE:CMD_READ;
			SDRAM_A <= { 4'b0010, addr_latch[0][9:1] };  // auto precharge
			SDRAM_BA <= {1'b0, addr_latch[0][23]};
			if (we_latch[0]) begin
				SDRAM_A[12:11] <= ~ds[0];
				sd_dq_out <= din_latch[0]; sd_dq_oe <= 1'b1;
				port1_ack <= port1_req;
			end
		end

		if(t == STATE_CAS1 && (we_latch[1] || oe_latch[1])) begin
			sd_cmd <= we_latch[1]?CMD_WRITE:CMD_READ;
			SDRAM_A <= { 4'b0010, addr_latch[1][9:1] };  // auto precharge
			SDRAM_BA <= {1'b1, addr_latch[1][23]};
			if (we_latch[1]) begin
				SDRAM_A[12:11] <= ~ds[1];
				sd_dq_out <= din_latch[1]; sd_dq_oe <= 1'b1;
				port2_ack <= port2_req;
			end
		end

		// Data returned
		if(t == STATE_READ0 && oe_latch[0]) begin
			case(port[0])
				PORT_REQ:  begin port1_q <= sd_din; port1_ack <= port1_req; end
				PORT_CPU1: begin cpu1_q  <= sd_din; end
				PORT_CPU2: begin cpu2_q  <= sd_din; end
				PORT_CPU3: begin cpu3_q  <= sd_din; end
				default: ;
			endcase;
		end

		// sp has no ack handshake, so its consumer (a slower synchronous
		// clock) can sample sp_q on ANY cycle - including between the two
		// burst beats. Upstream wrote sp_q[15:0] here and [31:16] one cycle
		// later at READ1b, leaving a window where sp_q is half new word,
		// half stale. Buffer the first beat and commit all 32 bits in one
		// cycle at READ1b instead. (port2_q keeps the two-stage update: its
		// consumers wait for port2_ack, which rises with the second beat.)
		if(t == STATE_READ1 && oe_latch[1]) begin
			case(port[1])
				PORT_REQ:	port2_q[15:0] <= sd_din;
				PORT_SP :    sp_q_lo <= sd_din;
				default: ;
			endcase;
		end

		if(t == STATE_READ1b && oe_latch[1]) begin
			case(port[1])
				PORT_REQ: begin port2_q[31:16] <= sd_din; port2_ack <= port2_req; end
				PORT_SP : begin    sp_q <= { sd_din, sp_q_lo }; end
				default: ;
			endcase;
		end
	end
end

// SDRAM_CLK forwarded through a Gowin ODDR (was Altera altddio_out).
// PHASE (the one bring-up knob): D0=1/D1=0 -> pin follows clk (0 deg fwd).
// The initial D0=0/D1=1 (180 deg) failed on hardware - the memtest reported
// the module responding but returning wrong read data (c0, got != expected),
// the textbook wrong-phase symptom - so this is flipped to 0 deg.
ODDR sdramclk_ddr (
	.Q0(SDRAM_CLK),
	.Q1(),
	.D0(1'b1),
	.D1(1'b0),
	.TX(1'b0),
	.CLK(clk_fwd)
);

endmodule
