alanswx/Arcade-MCR2-TangFPGA/src/rtl/mcr3scroll.vhd

---------------------------------------------------------------------------------
-- MCR3Scroll by Dar (darfpga@aol.fr) (06/12/2019)
-- http://darfpga.blogspot.fr
---------------------------------------------------------------------------------
--
-- release rev 00 : initial release
--  (06/12/2019)
--
---------------------------------------------------------------------------------
-- gen_ram.vhd & io_ps2_keyboard
-------------------------------- 
-- Copyright 2005-2008 by Peter Wendrich (pwsoft@syntiac.com)
-- http://www.syntiac.com/fpga64.html
---------------------------------------------------------------------------------
-- T80/T80se - Version : 304
-----------------------------
-- Z80 compatible microprocessor core
-- Copyright (c) 2001-2002 Daniel Wallner (jesus@opencores.org)
---------------------------------------------------------------------------------
-- YM2149 (AY-3-8910)
-- Copyright (c) MikeJ - Jan 2005
---------------------------------------------------------------------------------
-- Educational use only
-- Do not redistribute synthetized file with roms
-- Do not redistribute roms whatever the form
-- Use at your own risk
---------------------------------------------------------------------------------

--  Features :
--   Video        : VGA 31Khz/60Hz progressive and TV 15kHz interlaced
--   Coctail mode : NO
--   Sound        : OK - missing cheap/chip squeak deluxe board

--  MCR3Scroll (midway mcr) Hardware caracteristics :
--
--  VIDEO : 1xZ80@3MHz CPU accessing its program rom, working ram,
--    sprite data ram, I/O, sound board register and trigger.
--		  56Kx8bits program rom
--
--    One char tile map 30x32 tiles of 8x8 pixels 
--      1x4Kx8bits graphics rom 2bits/pixel single hard wired color set 

--    One scroling background tile map 16x64 tile of 8x32 pixels
--      2x16Kx8bits graphics rom 4bits/pixel single color set
--      rbg programmable ram palette 64 (16 for background) colors 9bits : 3red 3green 3blue
--
--    128 sprites, up to ~30/line, 32x32 with flip H/V
--      4x32Kx8bits graphics rom 4bits/pixel single color set
--      rbg programmable ram palette 64 (16 for sprites) colors 9bits : 3red 3green 3blue 
--
--    Working ram : 2Kx8bits
--    video char ram  : 1Kx8bits
--    video background ram  : 2Kx8bits
--    Sprites ram : 512x8bits + 512x8bits cache buffer

--    Sprites line buffer rams (graphics and colors) : 1 scan line delay flip/flop 2x256x8bits
--
--  SOUND : see tron_sound_board.vhd

---------------------------------------------------------------------------------
--  Schematics remarks :
--
--		Display is 512x480 pixels  (video 635x525 lines @ 20MHz )

--       635/20e6  = 31.75us per line  (31.750KHz)
--       31.75*525 = 16.67ms per frame (59.99Hz)
--        
--    Original video is interlaced 240 display lines per 1/2 frame
--
--       H0 and V0 are not use for background => each bg tile is 16x16 pixel but 
--			background graphics is 2x2 pixels defintion.
--
--			Sprite are 32x32 pixels with 1x1 pixel definition, 16 lines for odd 1/2
--       frame and 16 lines for even 2/2 frame thanks to V8 on sprite rom ROMAD2
--       (look at 74ls86 G1 pin 9 on video genration board schematics)
--
--    *H and V stand for Horizontal en Vertical counter (Hcnt, Vcnt in VHDL code)
--
--    /!\ For VHDL port interlaced video mode is replaced with progressive video 
--        mode.
--
--    Real hardware uses background ram access after each 1/2 frame (~line 240
--    and 480). In these areas cpu can access ram since scanlines are out of
--    visible display. In progessive mode there are video access around lines 240.
--    These accesses will create video artfacts aound mid display. In VHDL code
--    ram access is muliplexed between cpu and scanlines by using hcnt(0) in
--    order to avoid these artefacts.
--
--    Sprite data are stored first by cpu into a 'cache' buffer (staging ram at
--    K6/L6) this buffer is read and write for cpu. After visible display, cache
--    buffer (512x8) is moved to actual sprite ram buffer (512x8). Actual sprite
--    buffer is access by transfer address counter during 2 scanlines after 
--    visible area and only by sprite machine during visible area.
--
--    Thus cpu can read and update sprites position during entire frame except
--    during 2 lines.
-- 
--    Sprite data are organised (as seen by cpu F000-F1FF) into 128 * 4bytes.
--    bytes #1 : Vertical position
--    bytes #2 : code and attribute
--    bytes #3 : Horizontal position
--    bytes #4 : not used
--
--		Athough 1x1 pixel defintion sprite position horizontal/vertical is made on
--    on a 2x2 grid (due to only 8bits for position data)
--
--    Z80-CTC : interruption ar managed by CTC chip. ONly channel 3 is trigered
--    by hardware signal line 493. channel 0 to 2 are in timer mode. Schematic 
--    show zc/to of channel 0 connected to clk/trg of channel 1. This seems to be
--    unsued for that (Kick) game. 
--
--    Z80-CTC VHDL port keep separated interrupt controler and each counter so 
--    one can use them on its own. Priority daisy-chain is not done (not used in
--    that game). clock polarity selection is not done since it has no meaning
--    with digital clock/enable (e.g cpu_ena signal) method.
--
--    Ressource : input clock 40MHz is chosen to allow easy making of 20MHz for
--    pixel clock and 8MHz signal for amplitude modulation circuit of ssio board
--
--  TODO :
--    Working ram could be initialized to set initial difficulty level and
--    initial bases (live) number. Otherwise one can set it up by using service
--    menu at each power up.
--
---------------------------------------------------------------------------------

library ieee;
use ieee.std_logic_1164.all;
use ieee.std_logic_unsigned.all;
use ieee.numeric_std.all;

entity mcr3scroll is
-- Graphics-ROM baking and the CSD sound board, per board (2026-07-30). Same
-- discipline as mcr2.vhd/mcr1.vhd: defaults bake so a future standalone
-- MCR3Scroll board keeps working, while the merged 60K top passes an empty
-- name + GFX_LOADABLE => 1 so the bitstream carries NO ROM data (licensing,
-- TODO item 2). dpram needs LOADABLE whenever INIT_FILE is empty or its port B
-- silently goes read-only and the download dies with no error anywhere.
-- CSD_ENABLE => 0 removes the Cheap Squeak Deluxe board (68000 + PIA) for
-- Crater Raider, which is SSIO-only; Spy Hunter and Turbo Tag need it.
generic(
 -- bg gfx generics are absent by design: those RAMs are HOISTED to the top
 -- (see bg_addr/bg1_do/bg2_do below). Only the CHAR plane is still inside.
 CH_INIT      : string  := "rom_gfx_ch.hex";
 GFX_LOADABLE : integer := 0;
 CSD_ENABLE   : integer := 1;
 -- Sprite line buffers: 256x8 each, so an 18 Kb BSRAM block per buffer is
 -- almost entirely wasted. SPRLINE_RAMSTYLE lets a board move them to LUT RAM
 -- instead; the merged 3-family build has TEN across its cores and needs the
 -- blocks. Default "block_ram" keeps every existing board bit-identical.
 SPRLINE_RAMSTYLE : string := "block_ram";
 -- See the scratch-RAM ports below.
 SCRATCH_EXTERNAL : integer := 0;
 -- video_ram is split out so a board can hoist the small scratch RAMs but let
 -- a core keep its OWN video RAM. The merged build does that for MCR-3: at
 -- four cores the 4:1 mux on this RAM's CPU-side address sat on the critical
 -- path, and one BSRAM block buys the margin back.
 VRAM_EXTERNAL    : integer := 0
);
port(
  clock_40       : in  std_logic;
  reset          : in  std_logic;
  tv15Khz_mode   : in  std_logic;
  video_r        : out std_logic_vector(2 downto 0);
  video_g        : out std_logic_vector(2 downto 0);
  video_b        : out std_logic_vector(2 downto 0);
  video_csync    : out std_logic;
  video_hblank   : out std_logic;
  video_Vblank   : out std_logic;
  video_hs       : out std_logic;
  video_vs       : out std_logic;
  video_ce       : out std_logic;
  -- Local addition (matches src/rtl/mcr2.vhd / mcr1.vhd): expose the raster
  -- counter so the Tang top can align the framebuffer capture window; the
  -- video scanner is the same 633-wrap design as the other cores.
  hcnt_out       : out std_logic_vector(9 downto 0);
  vcnt_out       : out std_logic_vector(9 downto 0);
  cpu_halt_n     : out std_logic;   -- T80 HALT export (boot wedge watchdog)

  mod_crater     : in  std_logic;
  mod_turbo      : in  std_logic;

  separate_audio : in  std_logic;
  audio_out_l    : out std_logic_vector(15 downto 0);
  audio_out_r    : out std_logic_vector(15 downto 0);
  csd_audio_out  : out std_logic_vector( 9 downto 0);

  input_0        : in  std_logic_vector( 7 downto 0);
  input_1        : in  std_logic_vector( 7 downto 0);
  input_2        : in  std_logic_vector( 7 downto 0);
  input_3        : in  std_logic_vector( 7 downto 0);
  input_4        : in  std_logic_vector( 7 downto 0);
  output_4       : out std_logic_vector(7 downto 0);
  show_lamps     : in  std_logic; 
  
  cpu_rom_addr   : out std_logic_vector(15 downto 0);
  cpu_rom_do     : in  std_logic_vector( 7 downto 0);
  snd_rom_addr   : out std_logic_vector(13 downto 0);
  snd_rom_do     : in  std_logic_vector( 7 downto 0);
  csd_rom_addr   : out std_logic_vector(14 downto 1);
  csd_rom_do     : in  std_logic_vector(15 downto 0);
  sp_addr        : out std_logic_vector(14 downto 0);
  sp_graphx32_do : in  std_logic_vector(31 downto 0);

  -- Background tile graphics, HOISTED OUT of the core (2026-07-30), exactly as
  -- mcr3.vhd's were on 2026-07-27: the merged multi-family top shares ONE pair
  -- of 16 KB RAMs between cores, since only one core runs at a time, and these
  -- are 16 of the blocks that decide whether the merge fits at all. Pure port
  -- move - same 1-cycle read on the same inverted clock, so tile timing is
  -- untouched. The top owns the RAMs and the dl write decode, and must clock
  -- port A on NOT clock_40 (this core reads them on clock_vidn).
  -- NOTE the wiring is UNCROSSED here, unlike mcr3.vhd: upstream MCR3Scroll
  -- has bg_graphics_1 (rom_gfx1_1.hex, dl range "00") drive bg_graphx1_do,
  -- whereas upstream MCR-3 crosses them. Keep this straight or bg tiles get
  -- right shapes with wrong colours - see CLAUDE.md's per-core plane-order note.
  bg_addr        : out std_logic_vector(13 downto 0);
  bg1_do         : in  std_logic_vector( 7 downto 0);  -- RAM holding blob gfx1_1
  bg2_do         : in  std_logic_vector( 7 downto 0);  -- RAM holding blob gfx1_2

  dl_addr        : in  std_logic_vector(15 downto 0);
  dl_data        : in  std_logic_vector(7 downto 0);
  dl_wr          : in  std_logic;
  dl_din         : out std_logic_vector(7 downto 0);
  dl_nvram       : in  std_logic;
  dl_nvram_wr    : in  std_logic;

 -- SHARED SCRATCH RAM (SCRATCH_EXTERNAL => 1). The work RAM and the two sprite
 -- staging RAMs are byte-identical in mcr1/mcr2/mcr3/mcr3scroll, and only one
 -- core is ever out of reset, so the merged build keeps ONE set in the top
 -- instead of four. The top MUST mux we/addr/d by the running family: a core
 -- held in reset can still present a combinational write-enable, and that
 -- would corrupt the active game's RAM.
 -- `sh_` prefix because wram_we / sp_ram_we are internal signal names here.
 sh_wram_addr   : out std_logic_vector(10 downto 0);
 sh_wram_we     : out std_logic;
 sh_wram_d      : out std_logic_vector( 7 downto 0);
 sh_wram_q      : in  std_logic_vector( 7 downto 0) := (others => '0');
 sh_spr_addr    : out std_logic_vector( 8 downto 0);
 sh_spr_we      : out std_logic;
 sh_spr_d       : out std_logic_vector( 7 downto 0);
 sh_spr_q       : in  std_logic_vector( 7 downto 0) := (others => '0');
 sh_sprc_addr   : out std_logic_vector( 8 downto 0);
 sh_sprc_we     : out std_logic;
 sh_sprc_d      : out std_logic_vector( 7 downto 0);
 sh_sprc_q      : in  std_logic_vector( 7 downto 0) := (others => '0');
 sh_vram_addr   : out std_logic_vector(10 downto 0);
 sh_vram_we     : out std_logic;
 sh_vram_d      : out std_logic_vector( 7 downto 0);
 sh_vram_q      : in  std_logic_vector( 7 downto 0) := (others => '0')

 );
end mcr3scroll;

architecture struct of mcr3scroll is

 signal reset_n   : std_logic;
 signal clock_vid : std_logic;
 signal clock_vidn: std_logic;
 signal clock_cnt : std_logic_vector(3 downto 0) := "0000";

 signal hcnt    : std_logic_vector(9 downto 0) := (others=>'0'); -- horizontal counter
 signal hflip   : std_logic_vector(9 downto 0) := (others=>'0'); -- horizontal counter flip
 signal vcnt    : std_logic_vector(9 downto 0) := (others=>'0'); -- vertical counter
 signal vflip   : std_logic_vector(9 downto 0) := (others=>'0'); -- vertical counter flip
 signal shpos   : std_logic_vector(9 downto 0);
  
 signal hs_cnt, vs_cnt :std_logic_vector(9 downto 0) ;
 signal hsync0, hsync1, hsync2, hsync3, hsync4 : std_logic;
 signal top_frame : std_logic := '0';
 
 signal pix_ena     : std_logic;
 signal cpu_ena     : std_logic;

 signal cpu_addr    : std_logic_vector(15 downto 0);
 signal cpu_di      : std_logic_vector( 7 downto 0);
 signal cpu_do      : std_logic_vector( 7 downto 0);
 signal cpu_wr_n    : std_logic;
 signal cpu_rd_n    : std_logic;
 signal cpu_mreq_n  : std_logic;
 signal cpu_ioreq_n : std_logic;
 signal cpu_irq_n   : std_logic;
 signal cpu_m1_n    : std_logic;
 signal cpu_int_ack_n : std_logic;

 signal ctc_ce      : std_logic;
 signal ctc_do      : std_logic_vector(7 downto 0);

 signal ctc_counter_1_trg : std_logic;
 signal ctc_counter_2_trg : std_logic;
 signal ctc_counter_3_trg : std_logic;
 
 signal wram_we     : std_logic;
 signal wram_do     : std_logic_vector( 7 downto 0);
 
 signal ch_ram_addr : std_logic_vector(9 downto 0);
 signal ch_ram_we   : std_logic;
 signal ch_ram_do   : std_logic_vector(7 downto 0);
 signal ch_ram_do_r : std_logic_vector(7 downto 0); -- registred ram data for cpu
 
 signal ch_code      : std_logic_vector( 7 downto 0);
 signal ch_code_line : std_logic_vector(11 downto 0);
 signal ch_graphx_do : std_logic_vector( 7 downto 0);
 signal ch_color     : std_logic_vector( 1 downto 0);
 
 signal hoffset      : std_logic_vector(10 downto 0);
 signal hshift       : std_logic_vector(11 downto 0);
 signal voffset      : std_logic_vector( 8 downto 0);
 signal vshift       : std_logic_vector( 9 downto 0);

 signal bg_ram_addr  : std_logic_vector(10 downto 0);
 signal bg_ram_we    : std_logic;
 signal bg_ram_do    : std_logic_vector(7 downto 0);
 signal bg_ram_do_r  : std_logic_vector(7 downto 0); -- registred ram data for cpu

 signal bg_code      : std_logic_vector(7 downto 0); 
 signal bg_color     : std_logic_vector(3 downto 0); 

 signal bg_code_line    : std_logic_vector(13 downto 0);
 signal bg_graphx1_do   : std_logic_vector( 7 downto 0);
 signal bg_graphx2_do   : std_logic_vector( 7 downto 0);
 signal bg_palette_addr : std_logic_vector( 5 downto 0);
 
 signal sp_ram_cache_addr       : std_logic_vector(8 downto 0);
 signal sp_ram_cache_we         : std_logic;
 signal sp_ram_cache_do         : std_logic_vector(7 downto 0);
 signal sp_ram_cache_do_r       : std_logic_vector(7 downto 0);-- registred ram data for cpu
 
 signal move_buf          : std_logic;
 signal sp_ram_addr       : std_logic_vector(8 downto 0);
 signal sp_ram_we         : std_logic;
 signal sp_ram_do         : std_logic_vector(7 downto 0);

 signal sp_cnt          : std_logic_vector( 6 downto 0);
 signal sp_code         : std_logic_vector( 7 downto 0);
 signal sp_attr         : std_logic_vector( 7 downto 0);
 signal sp_input_phase  : std_logic_vector( 5 downto 0);

 signal sp_done         : std_logic;
 signal sp_vcnt         : std_logic_vector( 9 downto 0);
 signal sp_line         : std_logic_vector( 4 downto 0);
 signal sp_hcnt         : std_logic_vector( 8 downto 0); -- lsb used to mux rd/wr line buffer
 signal sp_on_line      : std_logic;
 signal sp_on_line_r    : std_logic;
 signal sp_byte_cnt     : std_logic_vector( 1 downto 0);
 signal sp_code_line    : std_logic_vector(14 downto 0);
 signal sp_code_line_mux: std_logic_vector(16 downto 0);
 signal sp_hflip        : std_logic_vector( 1 downto 0);
 signal sp_vflip        : std_logic_vector( 4 downto 0);
 
 signal sp_graphx_do    : std_logic_vector( 7 downto 0);  -- from internal roms
 signal sp_graphx32_do_r: std_logic_vector(31 downto 0);
 signal sp_graphx_mux   : std_logic_vector( 7 downto 0);
 signal sp_mux_roms     : std_logic_vector( 1 downto 0);
 
 signal sp_graphx_a     : std_logic_vector( 3 downto 0);
 signal sp_graphx_b     : std_logic_vector( 3 downto 0);
 signal sp_graphx_a_ok  : std_logic;
 signal sp_graphx_b_ok  : std_logic;
 
 signal sp_buffer_ram1_addr : std_logic_vector(7 downto 0);
 signal sp_buffer_ram1a_we  : std_logic;
 signal sp_buffer_ram1b_we  : std_logic;
 signal sp_buffer_ram1a_di  : std_logic_vector( 7 downto 0);
 signal sp_buffer_ram1b_di  : std_logic_vector( 7 downto 0);
 signal sp_buffer_ram1a_do  : std_logic_vector( 7 downto 0);
 signal sp_buffer_ram1b_do  : std_logic_vector( 7 downto 0);
 signal sp_buffer_ram1_do_r : std_logic_vector(15 downto 0);
 
 signal sp_buffer_ram2_addr : std_logic_vector(7 downto 0);
 signal sp_buffer_ram2a_we  : std_logic;
 signal sp_buffer_ram2b_we  : std_logic;
 signal sp_buffer_ram2a_di  : std_logic_vector( 7 downto 0);
 signal sp_buffer_ram2b_di  : std_logic_vector( 7 downto 0);
 signal sp_buffer_ram2a_do  : std_logic_vector( 7 downto 0);
 signal sp_buffer_ram2b_do  : std_logic_vector( 7 downto 0);
 signal sp_buffer_ram2_do_r : std_logic_vector(15 downto 0);
 
 signal sp_buffer_sel       : std_logic;
 
 signal mirr                : std_logic_vector(9 downto 0);
 signal sp_vid              : std_logic_vector(3 downto 0);
 signal sp_col              : std_logic_vector(3 downto 0);
-- signal sp_palette_addr     : std_logic_vector(5 downto 0);
 
 signal palette_addr        : std_logic_vector(5 downto 0);
 signal palette_we          : std_logic;
 signal palette_do          : std_logic_vector(8 downto 0);

 signal ssio_iowe : std_logic;
 signal ssio_do   : std_logic_vector(7 downto 0);

 signal out_4  : std_logic_vector(7 downto 0);

 signal lamp_oil       : std_logic;
 signal lamp_missile   : std_logic;
 signal lamp_van       : std_logic;
 signal lamp_smoke     : std_logic;
 signal lamp_gun       : std_logic;
 
 type texte is array(0 to  31) of std_logic_vector(7 downto 0);
 signal lamp_text: texte := (
	x"00", x"49", x"48", x"00",                             -- hi/lo
	x"4E", x"41", x"56", x"00",                             -- van
	x"45", x"4B", x"4F", x"4D", x"53", x"00",               -- smoke  
	x"4E", x"55", x"47", x"00",                             -- gun
	x"45", x"4C", x"49", x"53", x"53", x"49", x"4D", x"00", -- missile
   x"4C", x"49", x"4F", x"00",                             -- oil
	x"00", x"00");
  
 signal dl_cg_graphics_we   : std_logic;

begin

mirr <= (others => mod_crater);

clock_vid  <= clock_40;
clock_vidn <= not clock_40;
reset_n    <= not reset;

-- make enables clock from clock_vid
process (clock_vid, reset)
begin
	if reset='1' then
		clock_cnt <= (others=>'0');
	else 
		if rising_edge(clock_vid) then
			if clock_cnt = "1111" then  -- divide by 16
				clock_cnt <= (others=>'0');
			else
				clock_cnt <= clock_cnt + 1;
			end if;
		end if;
	end if;   		
end process;
--
cpu_ena <= '1' when clock_cnt(2 downto 0) = "111" else '0'; -- (5MHz for 91490 super cpu board)
pix_ena <= '1' when (clock_cnt(1 downto 0) = "11" and tv15Khz_mode = '1') or         -- (10MHz)
						  (clock_cnt(0) = '1'           and tv15Khz_mode = '0') else '0';  -- (20MHz)
video_ce <= pix_ena;
-----------------------------------
-- Video scanner  634x525 @20Mhz --
-- display 512x480               --
-----------------------------------
process (reset, clock_vid)
begin
	if reset='1' then
		hcnt  <= (others=>'0');
		vcnt  <= (others=>'0');
		top_frame <= '0';
	else 
		if rising_edge(clock_vid) then
			if pix_ena = '1' then
		
				hcnt <= hcnt + 1;
				if hcnt = 633 then
					hcnt <= (others=>'0');
					vcnt <= vcnt + 1;
					if (vcnt = 524 and tv15Khz_mode = '0') or (vcnt = 263 and tv15Khz_mode = '1') then
						vcnt <= (others=>'0');
						top_frame <= not top_frame;
					end if;
				end if;
			
				if tv15Khz_mode = '0' then 
					--	progessive mode
				
					-- tune 31kHz vertical screen position here
					if vcnt = 490-1 then video_vs <= '0'; end if; -- front porch 10
					if vcnt = 492-1 then video_vs <= '1'; end if; -- sync pulse   2
																				 -- back porch  33 
					-- tune 31kHz horizontal screen position here	
					if hcnt = 512+13+9+11 then video_hs <= '0'; end if; -- front porch 16/25*20 = 13
					if hcnt = 512+90+9+11 then video_hs <= '1'; end if; -- sync pulse  96/25*20 = 77
																				       -- back porch  48/25*20 = 38
					video_hblank <= '1';
					if hcnt >= 2+16+16 and hcnt < 514+16-1 then
						video_hblank <= '0';
					end if;

					video_vblank <= '1';
					if vcnt >= 1 and vcnt < 480 then
						video_vblank <= '0';
					end if;

				else -- interlaced mode
				 
					if hcnt = 530+28 then            -- tune 15KHz horizontal screen position here
						hs_cnt <= (others => '0');
						if (vcnt = 240) then          -- tune 15KHz vertical screen position here
							vs_cnt <= (others => '0');
						else
							vs_cnt <= vs_cnt +1;
						end if;
						
						--if vcnt = 240 then video_vs <= '0'; end if;
						--if vcnt = 242 then video_vs <= '1'; end if;

					else 
						hs_cnt <= hs_cnt + 1;
					end if;
					
					video_hblank <= '1';
					if hcnt >= 2+16+16 and ((hcnt < 514+16-1 and mod_crater = '0') or (hcnt < 514-1 and mod_crater = '1')) then
						video_hblank <= '0';
					end if;

					video_vblank <= '1';
					if vcnt >= 1 and vcnt < 241 then
						video_vblank <= '0';
					end if;
				
					if    hs_cnt =  0 then hsync0 <= '0';
					elsif hs_cnt = 47 then hsync0 <= '1';
					end if;

					if    hs_cnt =      0  then hsync1 <= '0';
					elsif hs_cnt =     23  then hsync1 <= '1';
					elsif hs_cnt = 317+ 0  then hsync1 <= '0';
					elsif hs_cnt = 317+23  then hsync1 <= '1';
					end if;
			
					if    hs_cnt =      0  then hsync2 <= '0';
					elsif hs_cnt = 317-47  then hsync2 <= '1';
					elsif hs_cnt = 317     then hsync2 <= '0';
					elsif hs_cnt = 634-47  then hsync2 <= '1';
					end if;

					
					if    hs_cnt =      0  then hsync3 <= '0';
					elsif hs_cnt =     23  then hsync3 <= '1';
					elsif hs_cnt = 317     then hsync3 <= '0';
					elsif hs_cnt = 634-47  then hsync3 <= '1';
					end if;

					if    hs_cnt =      0  then hsync4 <= '0';
					elsif hs_cnt = 317-47  then hsync4 <= '1';
					elsif hs_cnt = 317     then hsync4 <= '0';
					elsif hs_cnt = 317+23  then hsync4 <= '1';
					end if;
					
					
					if     vs_cnt =  1 then video_csync <= hsync1;
					elsif  vs_cnt =  2 then video_csync <= hsync1;
					elsif  vs_cnt =  3 then video_csync <= hsync1;
					elsif  vs_cnt =  4 and top_frame = '1' then video_csync <= hsync3;
					elsif  vs_cnt =  4 and top_frame = '0' then video_csync <= hsync1;
					elsif  vs_cnt =  5 then video_csync <= hsync2;
					elsif  vs_cnt =  6 then video_csync <= hsync2;
					elsif  vs_cnt =  7 and  top_frame = '1' then video_csync <= hsync4;
					elsif  vs_cnt =  7 and  top_frame = '0' then video_csync <= hsync2;
					elsif  vs_cnt =  8 then video_csync <= hsync1;
					elsif  vs_cnt =  9 then video_csync <= hsync1;
					elsif  vs_cnt = 10 then video_csync <= hsync1;
					elsif  vs_cnt = 11 then video_csync <= hsync0;
					else                    video_csync <= hsync0;
					end if;				
				
					if vcnt = 244 then video_vs <= '0'; end if;
					if vcnt = 248 then video_vs <= '1'; end if;
					if hcnt = 512+00+53 then video_hs <= '0'; end if;
					if hcnt = 512+47+53 then video_hs <= '1'; end if;
				end if;
			end if;
		end if;
	end if;
end process;

--------------------
-- players inputs --
--------------------
-- "11" for test & tilt & unused
-- input_0 <= not service & "11" & not shift & "11" & not coin2 & not coin1;
-- input_1 <= "111" & not gun & not smoke & not van & not missile &  not oil;
-- input_2 <= steering when output_4(7) = '1' else gas;
-- input_3 <= "111111" & demo_sound & timer;
-- input_4 <= x"FF";

-- ssio ouput_4 :
-- OP4 bit 0/3 J5-10/13 md0/3 (to cheap squeak deluxe and lamps)
-- OP4 bit  4  J5-14    st0   (to cheap squeak deluxe)
-- OP4 bit  5  J5-15    st1   (to lamps)
-- OP4 bit  6  J5-16    ard   (to absolute position)
-- OP4 bit  7  J5-17    sel   (to absolute position)

-------------------
-- lamps outputs --
-------------------
-- lamp board :
-- J1 12-10-11-14 md0-md3      (md0-md2 => A0-A2; md3 => data)
-- J1 13          st1          (write strobe)
-- J1  7          lamp oil     (A0-A2 : 0)
-- J1  8          lamp missile (A0-A2 : 1)
-- J1  6          lamp van     (A0-A2 : 2)
-- J1  5          lamp smoke   (A0-A2 : 3)
-- J1  3          lamp gun     (A0-A2 : 4)

process (clock_vid)
begin
	if rising_edge(clock_vid) then
		if out_4(5) = '0' then 
			if out_4(2 downto 0) = 0 then lamp_oil     <= out_4(3); end if;
			if out_4(2 downto 0) = 1 then lamp_missile <= out_4(3); end if;
			if out_4(2 downto 0) = 2 then lamp_van     <= out_4(3); end if;
			if out_4(2 downto 0) = 3 then lamp_smoke   <= out_4(3); end if;
			if out_4(2 downto 0) = 4 then lamp_gun     <= out_4(3); end if;
		end if;
	end if;
end process;
------------------------------------------
-- cpu data input with address decoding --
------------------------------------------
cpu_di <= cpu_rom_do   		 when cpu_mreq_n = '0' and cpu_addr(15 downto 12) < X"E" else    -- 0000-DFFF             56Ko
			 bg_ram_do_r       when cpu_mreq_n = '0' and (cpu_addr and x"F800") = x"E000" else -- video  ram  E000-E7FF  2Ko
			 ch_ram_do_r       when cpu_mreq_n = '0' and (cpu_addr and x"FC00") = x"E800" else -- char   ram  E800-EBFF  1Ko + mirroring 0400
			 wram_do     		 when cpu_mreq_n = '0' and (cpu_addr and X"F800") = x"F000" else -- work   ram  F000-F7FF  2Ko
			 sp_ram_cache_do_r when cpu_mreq_n = '0' and (cpu_addr and x"FE00") = x"F800" else -- sprite ram  F800-F9FF 512o  
			 ctc_do            when cpu_int_ack_n = '0' or ctc_ce = '1'                   else -- ctc (interrupt vector or counter data)
			 ssio_do           when cpu_ioreq_n = '0' and cpu_addr(7 downto 5) = "000" else    -- 0x00-0x1F
   		 X"FF";

------------------------------------------
-- write enable / ram access from CPU --
------------------------------------------
bg_ram_we       <= '1' when cpu_mreq_n = '0' and cpu_wr_n = '0' and (cpu_addr and x"F800") = x"E000" and hcnt(0) = '0' else '0';
ch_ram_we       <= '1' when cpu_mreq_n = '0' and cpu_wr_n = '0' and (cpu_addr and x"FC00") = x"E800" and hcnt(0) = '0' else '0';
wram_we         <= '1' when cpu_mreq_n = '0' and cpu_wr_n = '0' and (cpu_addr and x"F800") = x"F000" else '0';
sp_ram_cache_we <= '1' when cpu_mreq_n = '0' and cpu_wr_n = '0' and (cpu_addr and x"FE00") = x"F800" and hcnt(0) = '0' else '0';
palette_we      <= '1' when cpu_mreq_n = '0' and cpu_wr_n = '0' and (cpu_addr and x"FE00") = x"FA00" else '0'; -- 0xFA00-FA7F + mirroring 0x0180

ssio_iowe <= '1' when cpu_wr_n = '0' and cpu_ioreq_n = '0' else '0';

------------------------------------------------------------------------
-- Misc registers : ctc write enable / interrupt acknowledge
------------------------------------------------------------------------
cpu_int_ack_n     <= cpu_ioreq_n or cpu_m1_n;
ctc_ce            <= '1' when cpu_ioreq_n = '0' and cpu_addr(7 downto 4) = x"F" else '0';
ctc_counter_2_trg <= '1' when (vcnt >= 240 and vcnt <= 262 and tv15Khz_mode = '1') or (vcnt >= 480 and tv15Khz_mode = '0') else '0';
ctc_counter_3_trg <= '1' when top_frame = '1' and ((vcnt = 246 and tv15Khz_mode = '1') or (vcnt = 493 and tv15Khz_mode = '0')) else '0';

process (clock_vid)
begin
	if rising_edge(clock_vid) then

		if cpu_wr_n = '0' and cpu_ioreq_n = '0' then 
			if  cpu_addr(7 downto 0) = X"84" then hoffset( 7 downto 0) <= cpu_do;       end if;
			
			if  cpu_addr(7 downto 0) = X"85" then hoffset(10 downto 8) <= cpu_do(2 downto 0); 
															  voffset( 8)          <= cpu_do(7);    end if;
															  
			if  cpu_addr(7 downto 0) = X"86" then voffset( 7 downto 0) <= cpu_do;       end if;	
		end if;
	end if;
end process;

------------------------------------
---------- sprite machine ----------
----  91433 Video Gen III Board ----
------------------------------------
hflip <= hcnt xor mirr;
vflip <= vcnt(8 downto 0) & not top_frame when tv15Khz_mode = '1' else vcnt; -- do not apply mirror flip

sp_buffer_sel <= vflip(1) when tv15Khz_mode = '1' else vflip(0);

process (clock_vid)
begin
	if rising_edge(clock_vid) then
	
		if hcnt = 0 then
			sp_cnt <= (others => '0');
			sp_input_phase <= (others => '0');
			sp_on_line <= '0';
			sp_done <= '0';			
		end if;
				
		if sp_done = '0' then
			sp_input_phase <= sp_input_phase + 1 ;
			sp_hcnt <= sp_hcnt + 1;
			case sp_input_phase is
				when "000000" => 
					if sp_vcnt(8 downto 5) = x"F" then
						sp_line <= sp_vcnt(4 downto 0);
					else
						sp_input_phase <= (others => '0');
						sp_cnt <= sp_cnt + 1;
						if sp_cnt = "1111111" then sp_done <= '1'; end if;
					end if;
					sp_byte_cnt <= (others => '0');
				when "000001" => 
					sp_attr <= sp_ram_do;
				when "000010" => 
					sp_code <= sp_ram_do;
					sp_addr <= sp_ram_do(7 downto 0) & (sp_line xor sp_vflip) & (sp_byte_cnt xor sp_hflip); -- graphics rom addr
				when "000011" => 
					sp_hcnt <= sp_ram_do & '0';
				when "001010" => -- 10
					sp_graphx32_do_r <= sp_graphx32_do; -- latch incoming sprite data
					sp_addr <= sp_code(7 downto 0) & (sp_line xor sp_vflip) & (sp_byte_cnt+1 xor sp_hflip); -- advance graphics rom addr
					sp_on_line <= '1';
				when "010010"|"011010"|"100010" => -- 18,26,34
					sp_graphx32_do_r <= sp_graphx32_do; -- latch incoming sprite data
					sp_addr <= sp_code(7 downto 0) & (sp_line xor sp_vflip) & (sp_byte_cnt+2 xor sp_hflip); -- advance graphics rom addr
				  sp_byte_cnt <= sp_byte_cnt + 1;
				when "101010" => -- 42
					sp_on_line <= '0';
					sp_input_phase <= (others => '0');
					sp_cnt <= sp_cnt + 1;
					if sp_cnt = "1111111" then sp_done <= '1'; end if;
				when others =>
					null;
			end case;
			sp_mux_roms <= sp_input_phase(2 downto 1);
		end if;
			
		if pix_ena = '1' then 
			if hcnt(0) = '0' then
				sp_buffer_ram1_do_r <= sp_buffer_ram1b_do & sp_buffer_ram1a_do;
				sp_buffer_ram2_do_r <= sp_buffer_ram2b_do & sp_buffer_ram2a_do;
			end if;		
		end if;

	end if;
end process;

-- sp_ram_cache can be read/write by cpu when hcnt(0) = 0;
-- sp_ram_cache can be read by sprite machine when hcnt(0) = 1;

sp_ram_cache_addr <= cpu_addr(8 downto 0) when hcnt(0) = '0' else sp_ram_addr;

move_buf    <= '1' when (vcnt(8 downto 1) = 250 and tv15Khz_mode = '0') or (vcnt(7 downto 1) = 125 and tv15Khz_mode = '1') else '0'; -- line 500-501
sp_ram_addr <= vcnt(0) & hcnt(8 downto 1) when move_buf = '1' else sp_cnt & sp_input_phase(1 downto 0);
sp_ram_we   <= hcnt(0) when move_buf = '1' else '0';

sp_vcnt <= vflip + (sp_ram_do & '0') -1 ; -- valid when sp_input_phase = 0

sp_hflip <= (others => sp_attr(4));
sp_vflip <= (others => sp_attr(5));

sp_graphx_do <= sp_graphx32_do_r( 7 downto  0) when (sp_hflip(0) = '0' and sp_mux_roms = "01") or (sp_hflip(0) = '1' and sp_mux_roms = "00") else
                sp_graphx32_do_r(15 downto  8) when (sp_hflip(0) = '0' and sp_mux_roms = "10") or (sp_hflip(0) = '1' and sp_mux_roms = "11") else
					 sp_graphx32_do_r(23 downto 16) when (sp_hflip(0) = '0' and sp_mux_roms = "11") or (sp_hflip(0) = '1' and sp_mux_roms = "10") else
					 sp_graphx32_do_r(31 downto 24);-- when (sp_hflip(0) = '0' and sp_mux_roms = "00") or (sp_hflip(0) = '1' and sp_mux_roms = "01");

sp_graphx_a <= sp_graphx_do(7 downto 4) when sp_hflip(0) = '1' else sp_graphx_do(3 downto 0);
sp_graphx_b <= sp_graphx_do(3 downto 0) when sp_hflip(0) = '1' else sp_graphx_do(7 downto 4);

sp_graphx_a_ok <= '1' when sp_graphx_a /= x"0" else '0';
sp_graphx_b_ok <= '1' when sp_graphx_b /= x"0" else '0';

sp_buffer_ram1a_di  <= sp_attr(3 downto 0) & sp_graphx_a                when sp_buffer_sel = '1' else x"00";
sp_buffer_ram1b_di  <= sp_attr(3 downto 0) & sp_graphx_b                when sp_buffer_sel = '1' else x"00";
sp_buffer_ram1_addr <= sp_hcnt(8 downto 1)                              when sp_buffer_sel = '1' else hflip(8 downto 1) + x"0C" when mod_crater = '1' else hflip(8 downto 1) - x"04";
sp_buffer_ram1a_we  <= not sp_hcnt(0) and sp_on_line and sp_graphx_a_ok when sp_buffer_sel = '1' else hcnt(0);
sp_buffer_ram1b_we  <= not sp_hcnt(0) and sp_on_line and sp_graphx_b_ok when sp_buffer_sel = '1' else hcnt(0);

sp_buffer_ram2a_di  <= sp_attr(3 downto 0) & sp_graphx_a                when sp_buffer_sel = '0' else x"00";
sp_buffer_ram2b_di  <= sp_attr(3 downto 0) & sp_graphx_b                when sp_buffer_sel = '0' else x"00";
sp_buffer_ram2_addr <= sp_hcnt(8 downto 1)                              when sp_buffer_sel = '0' else hflip(8 downto 1) + x"0C" when mod_crater = '1' else hflip(8 downto 1) - x"04";
sp_buffer_ram2a_we  <= not sp_hcnt(0) and sp_on_line and sp_graphx_a_ok when sp_buffer_sel = '0' else hcnt(0);
sp_buffer_ram2b_we  <= not sp_hcnt(0) and sp_on_line and sp_graphx_b_ok when sp_buffer_sel = '0' else hcnt(0);

sp_vid <= sp_buffer_ram1_do_r(11 downto  8) when (sp_buffer_sel = '0') and (hflip(0) = '1') else
		    sp_buffer_ram1_do_r( 3 downto  0) when (sp_buffer_sel = '0') and (hflip(0) = '0') else
		    sp_buffer_ram2_do_r(11 downto  8) when (sp_buffer_sel = '1') and (hflip(0) = '1') else
			 sp_buffer_ram2_do_r( 3 downto  0);-- when (sp_buffer_sel = '1') and (hflip(0) = '0');

sp_col <= sp_buffer_ram1_do_r(15 downto 12) when (sp_buffer_sel = '0') and (hflip(0) = '1') else
          sp_buffer_ram1_do_r( 7 downto  4) when (sp_buffer_sel = '0') and (hflip(0) = '0') else
          sp_buffer_ram2_do_r(15 downto 12) when (sp_buffer_sel = '1') and (hflip(0) = '1') else
          sp_buffer_ram2_do_r( 7 downto  4);-- when (sp_buffer_sel = '1') and (hflip(0) = '0');

----------------------------
------- char machine -------
--- 91442 MCR III Board ----
----------------------------
ch_ram_addr <= cpu_addr(4 downto 0) & cpu_addr(9 downto 5) when hcnt(0) = '0' else vflip(8 downto 4) & hflip(8 downto 4);

ch_code_line <= ch_code & vflip(3 downto 1) & hflip(3);

process (clock_vid)
begin
	if rising_edge(clock_vid) then
	
		if pix_ena = '1' then
		
			if hcnt(0) = '1' then
				if hcnt(3 downto 1) = "111" then
					if hcnt(9 downto 4) = 31 then  -- add lamp text on last line
						ch_code <= lamp_text(to_integer(unsigned(vflip(8 downto 4))));
					else                           -- normal text
						ch_code <= ch_ram_do;
					end if;
				end if;
				
				case hflip(2 downto 1) is
					when "00" => ch_color <= ch_graphx_do(7 downto 6);
					when "01" => ch_color <= ch_graphx_do(5 downto 4);
					when "10" => ch_color <= ch_graphx_do(3 downto 2);
					when "11" => ch_color <= ch_graphx_do(1 downto 0);
				end case;
			end if;
		
		end if;

	end if;
end process;

----------------------------
---- background machine ----
--- 91442 MCR III Board ----
----------------------------
bg_ram_addr <= cpu_addr(10) & cpu_addr(3 downto 0) & cpu_addr(9 downto 4) when hcnt(0) = '0' else
					vshift(9 downto 5) & (hshift(11 downto 6) xor mirr(5 downto 0));

bg_code_line <= bg_code(7) & bg_code(5 downto 0) & (vshift(4 downto 1) xor (bg_code(6) & bg_code(6) & bg_code(6) & bg_code(6))) & (hshift(5 downto 3) xor mirr(5 downto 3));

shpos <= "1001011011" when mod_crater = '0' else "1001001001";

process (clock_vid)
begin
	if rising_edge(clock_vid) then
	
		-- catch ram data for cpu
		if hcnt(0) = '0' then
			ch_ram_do_r       <= ch_ram_do;
			bg_ram_do_r       <= bg_ram_do;
			sp_ram_cache_do_r <= sp_ram_cache_do;
		end if;

		if pix_ena = '1' then
		
			if hcnt = shpos then -- tune background h pos w.r.t char (use odd value to keep hshift(0) = hcnt(0))
				if mod_crater = '1' then
					hshift <= not (hoffset+296) & '0';
				elsif mod_turbo = '1' then
					hshift <= (hoffset+44) & '0'; 
				else
					hshift <= hoffset & '0'; 
				end if;
			else
				hshift <= hshift + 1 ;
			end if;
			
			if (vflip(9 downto 1) = "100000111"  and tv15Khz_mode = '1') or
				(vflip(9 downto 0) = "1000001100" and tv15Khz_mode = '0') then  -- tune background v pos w.r.t char
				vshift <= voffset & '0'; 
			else
				if hcnt = shpos then 
					if tv15Khz_mode = '0' then vshift <= vshift + 1; end if;
					if tv15Khz_mode = '1' then vshift <= vshift + 2; end if;
				end if;
			end if;
		
			if hcnt(0) = '1' then
				if hshift(5 downto 0) = "111111" then bg_code <= bg_ram_do; end if;	
				
				case (hshift(2 downto 1) xor mirr(2 downto 1)) is
					when "00" => bg_color <= bg_graphx2_do(7 downto 6) & bg_graphx1_do(7 downto 6);
					when "01" => bg_color <= bg_graphx2_do(5 downto 4) & bg_graphx1_do(5 downto 4);
					when "10" => bg_color <= bg_graphx2_do(3 downto 2) & bg_graphx1_do(3 downto 2);
					when "11" => bg_color <= bg_graphx2_do(1 downto 0) & bg_graphx1_do(1 downto 0);
				end case;
			end if;
		
		end if;

	end if;
end process;
	
---------------------------
-- mux char/sprite video --
---------------------------
palette_addr <= mod_crater & '1' & bg_color when sp_vid(2 downto 0) = "000" else
					 (not sp_col(1 downto 0) and (mod_crater & mod_crater)) & sp_vid;

process (clock_vid)
begin
	if rising_edge(clock_vid) then
		video_g <= palette_do(2 downto 0);
		video_b <= palette_do(5 downto 3);
		video_r <= palette_do(8 downto 6);
		
		if hcnt(9 downto 4) >= 32 then -- set lamp text line colors
		
			if ch_color = "11" and show_lamps = '1' then 
			  if (vflip >  1*16 and vflip <  4*16 and input_0(4) = '0') then 
					video_g <= "000";
					video_b <= "111";
					video_r <= "000";			  
			  elsif
				  (vflip >  4*16 and vflip <  8*16 and lamp_van     = '1') or
				  (vflip >  8*16 and vflip < 14*16 and lamp_smoke   = '1') or
				  (vflip > 14*16 and vflip < 18*16 and lamp_gun     = '1') or
				  (vflip > 18*16 and vflip < 26*16 and lamp_missile = '1') or
				  (vflip > 26*16 and vflip < 31*16 and lamp_oil     = '1') then 
					video_g <= "000";
					video_b <= "000";
					video_r <= "111";
				else
					video_g <= "010";  -- light grey for light OFF text
					video_b <= "010";
					video_r <= "010";
				end if;
			end if;
					
		else
		
			case ch_color is
				when "01" =>
					video_g <= "111";
					video_b <= "000";
					video_r <= "000";
				when "10" =>
					video_g <= "000";
					video_b <= "111";
					video_r <= "000";
				when "11" =>
					video_g <= "111";
					video_b <= "111";
					video_r <= "111";
				when others => null;	
			end case;

		end if;
		
	end if;
end process;		
		
------------------------------
-- components & sound board --
------------------------------

-- microprocessor Z80
cpu : entity work.T80s
generic map(Mode => 0, T2Write => 1, IOWait => 1)
port map(
  RESET_n => reset_n,
  CLK     => clock_vid,
  CEN     => cpu_ena,
  WAIT_n  => '1',
  INT_n   => cpu_irq_n,
  NMI_n   => '1', --cpu_nmi_n,
  BUSRQ_n => '1',
  M1_n    => cpu_m1_n,
  MREQ_n  => cpu_mreq_n,
  IORQ_n  => cpu_ioreq_n,
  RD_n    => cpu_rd_n,
  WR_n    => cpu_wr_n,
  RFSH_n  => open,
  HALT_n  => cpu_halt_n,
  BUSAK_n => open,
  A       => cpu_addr,
  DI      => cpu_di,
  DO      => cpu_do
);

-- Z80-CTC (MK3882)
z80ctc : entity work.z80ctc_top
port map (
	clock     => clock_vid,
	clock_ena => cpu_ena,
	reset     => reset,
	din       => cpu_do,
	cpu_din   => cpu_di,
	dout      => ctc_do,
	ce_n      => not ctc_ce,
	cs        => cpu_addr(1 downto 0),
	m1_n      => cpu_m1_n,
	iorq_n    => cpu_ioreq_n,
	rd_n      => cpu_rd_n,
	int_n     => cpu_irq_n,
	trg0      => '0',
	to0       => ctc_counter_1_trg,
	trg1      => ctc_counter_1_trg,
	to1       => open,
	trg2      => mod_crater and ctc_counter_2_trg,
	to2       => open,
	trg3      => ctc_counter_3_trg
);

cpu_rom_addr <= cpu_addr when cpu_addr < x"A000" else cpu_addr xor x"6000"; -- last rom has upper/lower part swapped

hcnt_out <= hcnt;   -- local addition: surface the raster counter (see entity)
vcnt_out <= vcnt;

-- Background tile graphics now live in the top (see the entity comment).
-- UNCROSSED, matching upstream MCR3Scroll's own instance ordering.
bg_addr       <= bg_code_line;
bg_graphx1_do <= bg1_do;
bg_graphx2_do <= bg2_do;

-- working RAM   F000-F7FF  2Ko
scratch_int : if SCRATCH_EXTERNAL = 0 generate
wram : entity work.dpram
generic map( dWidth => 8, aWidth => 11)
port map(
	clk_a  => clock_vidn,
	we_a   => wram_we,
	addr_a => cpu_addr(10 downto 0),
	d_a    => cpu_do,
	q_a    => wram_do,
 
	clk_b  => clock_vid,
	we_b   => (dl_wr or dl_nvram_wr) and dl_nvram,
	addr_b => dl_addr(10 downto 0),
	d_b    => dl_data(7 downto 0),
	q_b     => dl_din(7 downto 0)
);
end generate;

-- char RAM   E800-EBFF  1Ko + mirroring 0400
char_ram : entity work.gen_ram
generic map( dWidth => 8, aWidth => 10)
port map(
 clk  => clock_vidn,
 we   => ch_ram_we,
 addr => ch_ram_addr,
 d    => cpu_do,
 q    => ch_ram_do
);

-- video RAM   E000-E7FF  2Ko
vram_int : if VRAM_EXTERNAL = 0 generate
video_ram : entity work.gen_ram
generic map( dWidth => 8, aWidth => 11)
port map(
 clk  => clock_vidn,
 we   => bg_ram_we,
 addr => bg_ram_addr,
 d    => cpu_do,
 q    => bg_ram_do
);
end generate;
	
-- sprite RAM (no cpu access)
spr_int : if SCRATCH_EXTERNAL = 0 generate
sprite_ram : entity work.gen_ram
generic map( dWidth => 8, aWidth => 9)
port map(
 clk  => clock_vidn,
 we   => sp_ram_we,
 addr => sp_ram_addr,
 d    => sp_ram_cache_do,
 q    => sp_ram_do
);
end generate;

-- sprite RAM  F800-F9FF 512o 
sprc_int : if SCRATCH_EXTERNAL = 0 generate
sprites_ram_cache : entity work.gen_ram
generic map( dWidth => 8, aWidth => 9)
port map(
 clk  => clock_vidn,
 we   => sp_ram_cache_we,
 addr => sp_ram_cache_addr,
 d    => cpu_do,
 q    => sp_ram_cache_do
);
end generate;

-- HOISTED scratch RAM: the top owns one set for all four cores. Reads are the
-- same 1-cycle, same clock edge (the top clocks port A on NOT clock_40), so
-- this is a pure port move.
scratch_ext : if SCRATCH_EXTERNAL /= 0 generate
  sh_wram_addr    <= cpu_addr(10 downto 0);
  sh_wram_we      <= wram_we;
  sh_wram_d       <= cpu_do;
  wram_do         <= sh_wram_q;
  dl_din          <= (others => '0');   -- nvram read-back unused when hoisted

  sh_spr_addr     <= sp_ram_addr;
  sh_spr_we       <= sp_ram_we;
  sh_spr_d        <= sp_ram_cache_do;
  sp_ram_do       <= sh_spr_q;

  sh_sprc_addr    <= sp_ram_cache_addr;
  sh_sprc_we      <= sp_ram_cache_we;
  sh_sprc_d       <= cpu_do;
  sp_ram_cache_do <= sh_sprc_q;

end generate;

vram_ext : if VRAM_EXTERNAL /= 0 generate
  sh_vram_addr    <= bg_ram_addr;
  sh_vram_we      <= bg_ram_we;
  sh_vram_d       <= cpu_do;
  bg_ram_do       <= sh_vram_q;
end generate;


-- sprite line buffer 1a
sprlinebuf1a : entity work.gen_ram
generic map( dWidth => 8, aWidth => 8, RAMSTYLE => SPRLINE_RAMSTYLE)
port map(
 clk  => clock_vidn,
 we   => sp_buffer_ram1a_we,
 addr => sp_buffer_ram1_addr,
 d    => sp_buffer_ram1a_di,
 q    => sp_buffer_ram1a_do
);

-- sprite line buffer 1b
sprlinebuf1b : entity work.gen_ram
generic map( dWidth => 8, aWidth => 8, RAMSTYLE => SPRLINE_RAMSTYLE)
port map(
 clk  => clock_vidn,
 we   => sp_buffer_ram1b_we,
 addr => sp_buffer_ram1_addr,
 d    => sp_buffer_ram1b_di,
 q    => sp_buffer_ram1b_do
);

-- sprite line buffer 2a
sprlinebuf2a : entity work.gen_ram
generic map( dWidth => 8, aWidth => 8, RAMSTYLE => SPRLINE_RAMSTYLE)
port map(
 clk  => clock_vidn,
 we   => sp_buffer_ram2a_we,
 addr => sp_buffer_ram2_addr,
 d    => sp_buffer_ram2a_di,
 q    => sp_buffer_ram2a_do
);

-- sprite line buffer 2b
sprlinebuf2b : entity work.gen_ram
generic map( dWidth => 8, aWidth => 8, RAMSTYLE => SPRLINE_RAMSTYLE)
port map(
 clk  => clock_vidn,
 we   => sp_buffer_ram2b_we,
 addr => sp_buffer_ram2_addr,
 d    => sp_buffer_ram2b_di,
 q    => sp_buffer_ram2b_do
);

-- char graphics ROM 10G (Spy Hunter's status line / alpha plane)
ch_graphics : entity work.dpram
generic map(
	aWidth => 12,
	dWidth => 8,
	INIT_FILE => CH_INIT,            -- "" + LOADABLE on the 60K (no baked ROMs)
	LOADABLE  => GFX_LOADABLE
)
port map(
 clk_a  => clock_vidn,
 we_a   => '0',
 d_a    => x"00",
 addr_a => ch_code_line,
 q_a    => ch_graphx_do,
 clk_b  => clock_vid,
 addr_b => dl_addr(11 downto 0),
 we_b   => dl_cg_graphics_we,
 d_b    => dl_data,
 q_b    => open
);
dl_cg_graphics_we <= '1' when dl_wr = '1' and dl_addr(15 downto 12) = "1000" else '0';

-- background graphics ROMs 3A/4A + 5A/6A were HERE. They are now in the top
-- (bg_addr/bg1_do/bg2_do, wired at the top of the architecture) so the merged
-- multi-family build can share one pair across cores. Their dl decode moved
-- with them; dl_bg_graphics_{1,2}_we are gone.


-- background & sprite palette
palette : entity work.dpram
generic map( dWidth => 9, aWidth => 6)
port map(
 clk_a  => clock_vidn,
 we_a   => palette_we,
 addr_a => cpu_addr(6 downto 1),
 d_a    => cpu_addr(0) & cpu_do,

 clk_b  => clock_vidn,
 we_b   => '0',
 d_b    => "000000000",
 addr_b => palette_addr,
 q_b    => palette_do
);

sound_board : entity work.mcr_sound_board
port map(
 clock_40    => clock_40,
 reset       => reset,
 
 enable      => not mod_turbo,

 main_cpu_addr => cpu_addr(7 downto 0),
 
 ssio_iowe => ssio_iowe,
 ssio_di   => cpu_do,
 ssio_do   => ssio_do,
 
 input_0 => input_0,
 input_1 => input_1,
 input_2 => input_2,
 input_3 => input_3,
 input_4 => input_4,
 
 output_4 => out_4,
 cpu_rom_addr => snd_rom_addr,
 cpu_rom_do   => snd_rom_do,
 
 separate_audio => separate_audio,
 audio_out_l    => audio_out_l,
 audio_out_r    => audio_out_r
);

output_4 <= out_4;

-- Cheap Squeak Deluxe (68000 + PIA music board): Spy Hunter and Turbo Tag
-- only. Crater Raider is SSIO-only, so CSD_ENABLE => 0 leaves the whole
-- FX68K/PIA stack out of the build - the lever for measuring what it costs.
csd_gen : if CSD_ENABLE /= 0 generate
  csd: entity work.cheap_squeak_deluxe
  port map (
   clock_40 => clock_40,
   reset => reset or mod_crater,
   input => out_4,
   rom_addr => csd_rom_addr,
   rom_do => csd_rom_do,
   audio_out => csd_audio_out
  );
end generate;

no_csd_gen : if CSD_ENABLE = 0 generate
  csd_rom_addr  <= (others => '0');
  csd_audio_out <= (others => '0');
end generate;

end struct;
