alanswx/Arcade-MCR2-TangFPGA/src/rtl/sdram_cl2_2ch.v

// VENDORED 2026-07-24 from nand2mario/snestang src/sdram_cl2_2ch.v (unmodified)
// for the SDRAM retention experiment: does the KNOWN-GOOD controller retain
// data on our Tang SDRAM module where sdram_gw does not? Note snestang drives
// the SDRAM clock PIN from a 225-degree phase-shifted PLL output directly
// (assign O_sdram_clk = fclk_p) - NOT an ODDR at 0 degrees like sdram_gw.
//
// Double-channel CL2 SDRAM controller for SNES on Tang Mega 138K Pro
// nand2mario 2024.2
// 
// This supports two parallel access streams (ROM/WRAM/BSRAM/RISC-V softcore and ARAM), 
// independent from each other. SNES ROM/WRAM uses bank 0 (8MB, largest game is 6MB, 
// WRAM 1MB). RV and BSRAM uses bank 1. ARAM uses bank 2.
//
// This controller works at 64.5Mhz, lower than the 3 channel controller, making it
// more stable on the Mega 138K Pro.
//
// SDRAM is accessed in an interleaving style like this (RAS: bank activation,
//   CAS: read/write commands, DATA: read data available),
//
// clk_#    CPU         ARAM        clkref
//   0      RAS1                      1
//   1      CAS1        DATA2         0
//   2                  RAS2/Refresh  0
//   3                                0
//   4      DATA1       CAS2          1
//   5                                1
// 
// Here we do not overlap the two CAS-DATA periods, avoiding potential bus contentions.
//
// Requests are placed using the "multi-cycle req-ack handshake", borrowed from the MIST
// sdram controller. Whenever a new request is needed, the host readies the addr/din/we lines,
// then toggles the *_req line. After the controller accepts the request, it toggles the 
// *_ack line to notify the host. Now the host is free to make new requests.
//
// A clkref signal, if supplied, allows finer control of the timings of the controller.
// It needs to be 1/6 the speed of clk. The cycles will aligned as shown above.
// In this case, CPU/RV requests are accepted when clkref=1, while ARAM requests are
// accepted when clkref=0.
//
// Clkref also allows relaxed timing constraints. Requests need to be ready at most 2 
// clks after mclk edge (3 for CPU/RV). Data out is ready at least 3 fclk before mclk 
// posedge (TODO: current true only for BSRAM). This means the following timing constraints.
//
// set_multicycle_path 2 -setup -end -from [get_clocks {mclk}] -to [get_clocks {fclk}]
// set_multicycle_path 1 -hold -end -from [get_clocks {mclk}] -to [get_clocks {fclk}]
// set_multicycle_path 3 -setup -start -from [get_clocks {fclk}] -to [get_clocks {mclk}]
// set_multicycle_path 2 -hold -start -from [get_clocks {fclk}] -to [get_clocks {mclk}]
//
// Tang SDRAM v1.2 - Winbond W9825G6KH. 8K rows, 512 words per row, 16 bits per word

module sdram_snes
#(
    // Clock frequency, max 66.7Mhz with current set of T_xx/CAS parameters.
    parameter         FREQ = 64_800_000,  

    // Time delays for 66.7Mhz max clock (min clock cycle 15ns)
    // The SDRAM supports max 166.7Mhz (RP/RCD/RC need changes)
    // Alliance AS4C32M16SB-7TIN 512Mb
    parameter [3:0]   CAS  = 4'd2,     // 2/3 cycles, set in mode register
    parameter [3:0]   T_WR = 4'd2,     // 2 cycles, write recovery
    parameter [3:0]   T_MRD= 4'd2,     // 2 cycles, mode register set
    parameter [3:0]   T_RP = 4'd1,     // 15ns, precharge to active
    parameter [3:0]   T_RCD= 4'd1,     // 15ns, active to r/w
    parameter [3:0]   T_RC = 4'd4      // 63ns, ref/active to ref/active
)
(
    // SDRAM side interface
    inout  reg [15:0] SDRAM_DQ,
    output     [12:0] SDRAM_A,
    output reg [1:0]  SDRAM_DQM,
    output reg [1:0]  SDRAM_BA,
    output            SDRAM_nCS,
    output            SDRAM_nWE,
    output            SDRAM_nRAS,
    output            SDRAM_nCAS,
    output            SDRAM_CKE,    // not strictly necessary, always 1
    
    // Logic side interface
    input             clk,          // sdram clock, max 66.7Mhz
    input             mclk,
    input             clkref,       // main reference clock, half speed of clk
    input             resetn,

    // CPU access (ROM and WRAM) uses bank 0 and 1 (total 16MB)
	input      [15:0] cpu_din /* synthesis syn_keep=1 */,
	input             cpu_port,
	output reg [15:0] cpu_port0,    // output register for bank 0
	output reg [15:0] cpu_port1,    // output register for bank 1
	input      [22:1] cpu_addr,     // 8MB SNES memory, with WRAM at end
    input             cpu_req,
    output reg        cpu_req_ack,
	input             cpu_we,
	input       [1:0] cpu_ds,       // which bytes to enable

    input      [19:0] bsram_addr,   // only [16:0], max 128KB
    input       [7:0] bsram_din,    // byte access
    output reg  [7:0] bsram_dout,
    input             bsram_req,
    output reg        bsram_req_ack,
    input             bsram_we,

    // ARAM access uses bank 2
	input             aram_16,      // 16-bit access
	input      [15:0] aram_addr,
	input      [15:0] aram_din,
	output reg [15:0] aram_dout,
    input             aram_req,
    output reg        aram_req_ack,
	input             aram_we,

    // RISC-V softcore
    input      [22:1] rv_addr,      // 8MB RV memory space
    input      [15:0] rv_din,       // 16-bit accesses
    input      [1:0]  rv_ds,
    output reg [15:0] rv_dout,
    input             rv_req,
    output reg        rv_req_ack,   // ready for new requests. read data available on NEXT mclk
    input             rv_we,

    output reg [23:0] total_refresh,

    output reg        busy
);

// Tri-state DQ input/output
reg dq_oen;        // 0 means output
reg [15:0] dq_out;
assign SDRAM_DQ = dq_oen ? {16{1'bz}} : dq_out;
wire [15:0] dq_in = SDRAM_DQ;     // DQ input
reg [3:0] cmd;
reg [12:0] a;
assign {SDRAM_nCS, SDRAM_nRAS, SDRAM_nCAS, SDRAM_nWE} = cmd;
assign SDRAM_A = a;

assign SDRAM_CKE = 1'b1;

// CS# RAS# CAS# WE#
localparam CMD_NOP=4'b1111;
localparam CMD_SetModeReg=4'b0000;
localparam CMD_BankActivate=4'b0011;
localparam CMD_Write=4'b0100;
localparam CMD_Read=4'b0101;
localparam CMD_AutoRefresh=4'b0001;
localparam CMD_PreCharge=4'b0010;

localparam [2:0] BURST_LEN = 3'b0;      // burst length 1
localparam BURST_MODE = 1'b0;           // sequential
localparam [10:0] MODE_REG = {4'b0, CAS[2:0], BURST_MODE, BURST_LEN};
// 64ms/8192 rows = 7.8us -> 500 cycles@64.8MHz
localparam RFRSH_CYCLES = 9'd501;

// state
reg [11:0] cycle;       // one hot encoded
reg normal, setup;
reg cfg_now;            // pulse for configuration

// requests
reg [24:0] addr_latch[2];
reg [15:0] din_latch[2];
reg  [2:0] oe_latch;
reg  [2:0] we_latch;
reg  [1:0] ds[2];

localparam PORT_NONE  = 2'd0;

localparam PORT_CPU   = 2'd1;
localparam PORT_BSRAM = 2'd2;
localparam PORT_RV    = 2'd3;

localparam PORT_ARAM  = 2'd1;

reg  [1:0] port[2];
reg  [1:0] next_port[2];
reg [24:0] next_addr[2];        // 2-bit bank #, then 8MB byte address in bank
reg [15:0] next_din[2];
reg  [1:0] next_ds[2];
reg  [2:0] next_we;
reg  [2:0] next_oe;

reg clkref_r;
always @(posedge clk) clkref_r <= clkref;

// reg        refresh;
reg [8:0]  refresh_cnt;
reg        need_refresh = 1'b0;

always @(posedge clk) begin
	if (refresh_cnt == 0)
		need_refresh <= 0;
	else if (refresh_cnt == RFRSH_CYCLES)
		need_refresh <= 1;
end

// ROM: bank 0,1
// WRAM, BSRAM, RV: bank 1
always @(*) begin
	next_port[0] = PORT_NONE;
	next_addr[0] = 0;
	next_we[0] = 0;
	next_oe[0] = 0;
	next_ds[0] = 0;
	next_din[0] = 0;
	// if (refresh) next_port[0] = PORT_NONE; else 
    if (cpu_req ^ cpu_req_ack) begin
		next_port[0] = PORT_CPU;
		next_addr[0] = { 2'b00, cpu_addr, 1'b0 };       // CPU uses bank 0, WRAM at the end
		next_din[0]  = cpu_din;
		next_ds[0]   = cpu_ds;
		next_we[0]   = cpu_we;
		next_oe[0]   = ~cpu_we;
	end else if (bsram_req ^ bsram_req_ack) begin
		next_port[0] = PORT_BSRAM;
		next_addr[0] = { 5'b01_111, bsram_addr };       // BSRAM at start of 7MB of bank 1 (also accessible from RV)
		next_din[0] = { bsram_din, bsram_din };
		next_ds[0] = {bsram_addr[0], ~bsram_addr[0]};
		next_we[0] = bsram_we;
		next_oe[0] = ~bsram_we;
	end else if (rv_req ^ rv_req_ack) begin             // RV uses bank 1 and has lowest priority
		next_port[0] = PORT_RV;
		next_addr[0] = { 2'b01, rv_addr, 1'b0 };
		next_we[0] = rv_we;
		next_oe[0] = ~rv_we;
		next_din[0] = rv_din;
		next_ds[0] = rv_ds;
	end 
end

// ARAM: bank 2
always @* begin
	next_port[1] = PORT_NONE;
	next_addr[1] = 0;
	next_we[1] = 0;
	next_oe[1] = 0;
	next_ds[1] = 0;
	next_din[1] = 0;
//	if (refresh) next_port[1] <= PORT_NONE;	else 
    if (aram_req ^ aram_req_ack) begin
		next_port[1] = PORT_ARAM;
		next_addr[1] = { 9'b10_1111000, aram_addr };   // ARAM uses bank 2
		next_we[1]   = aram_we;
		next_oe[1]   = ~aram_we;
		next_din[1]  = aram_din;
		next_ds[1]   = aram_16 ? 2'b11 : {aram_addr[0], ~aram_addr[0]};
	end
end

reg [7:0] bsram_dout_reg;
assign bsram_dout = (cycle[4] && oe_latch[0] && port[0] == PORT_BSRAM) ? (ds[0][0] ? dq_in[7:0] : dq_in[15:8]) : bsram_dout_reg;

//
// SDRAM state machine
//
always @(posedge clk) begin
    if (~resetn) begin
        busy <= 1'b1;
        dq_oen <= 1;
        SDRAM_DQM <= 2'b0;
        normal <= 0;
        setup <= 0;
    end else begin
        // defaults
        dq_oen <= 1'b1;
        SDRAM_DQM <= 2'b11;
        cmd <= CMD_NOP; 

        // wait 200 us on power-on
        if (~normal && ~setup && cfg_now) begin // wait 200 us on power-on
            setup <= 1;
            cycle <= 1;
        end 

        // setup process
        if (setup) begin
            cycle <= {cycle[10:0], 1'b0};       // cycle 0-11 for setup
            // configuration sequence
            if (cycle[0]) begin
                // precharge all
                cmd <= CMD_PreCharge;
                a[10] <= 1'b1;
            end
            if (cycle[T_RP]) begin
                // 1st AutoRefresh
                cmd <= CMD_AutoRefresh;
            end
            if (cycle[T_RP+T_RC]) begin
                // 2nd AutoRefresh
                cmd <= CMD_AutoRefresh;
            end
            if (cycle[T_RP+T_RC+T_RC]) begin
                // set register
                cmd <= CMD_SetModeReg;
                a[10:0] <= MODE_REG;
            end
            if (cycle[T_RP+T_RC+T_RC+T_MRD]) begin
                setup <= 0;
                normal <= 1;
                cycle <= 1;
                busy <= 1'b0;               // init&config is done
            end
        end 
        if (normal) begin
            if (clkref & ~clkref_r)             // go to cycle 5 after clkref posedge
                cycle <= 12'b0000_0010_0000;
            else
                cycle[5:0] <= {cycle[4:0], cycle[5]};
            refresh_cnt <= refresh_cnt + 1'd1;
            
            // RAS
            // bank 0,1 - ROM, WRAM, BSRAM and RV
            if (cycle[0]) begin
    			port[0] <= next_port[0];
	    		{ we_latch[0], oe_latch[0] } <= { next_we[0], next_oe[0] };
    			addr_latch[0] <= next_addr[0];
	    		a <= next_addr[0][22:10];
                SDRAM_BA <= next_addr[0][24:23];
                din_latch[0] <= next_din[0];
                ds[0] <= next_ds[0];
                if (next_port[0] != PORT_NONE) cmd <= CMD_BankActivate;
            end

            // bank 2 - ARAM
            if (cycle[2]) begin
                port[1] <= next_port[1];
                { we_latch[1], oe_latch[1] } <= { next_we[1], next_oe[1] };
                addr_latch[1] <= next_addr[1];
                a <= next_addr[1][22:10];
                SDRAM_BA <= 2'b10;
                din_latch[1] <= next_din[1];
                ds[1] <= next_ds[1];
                if (next_port[1] != PORT_NONE) begin 
                    cmd <= CMD_BankActivate; 
                    aram_req_ack <= aram_req; 
                end else if (!we_latch[0] && !oe_latch[0] && !we_latch[1] && !oe_latch[1] && need_refresh) begin
                    // refresh <= 1'b1;
                    refresh_cnt <= 0;
                    cmd <= CMD_AutoRefresh;
                    total_refresh <= total_refresh + 1;
                end
            end

            // CAS
            // ROM, WRAM, BSRAM and RV
            if (cycle[1] && (oe_latch[0] || we_latch[0])) begin
                cmd <= we_latch[0]?CMD_Write:CMD_Read;
                if (we_latch[0]) begin
                    dq_oen <= 0;
                    dq_out <= din_latch[0];
                    SDRAM_DQM <= ~ds[0];
                end else
                    SDRAM_DQM <= 2'b00;
                a <= { 4'b0010, addr_latch[0][9:1] };  // auto precharge
                SDRAM_BA <= addr_latch[0][24:23];                
            end
            if (cycle[1]) begin
                case (port[0])
                PORT_CPU:   cpu_req_ack <= cpu_req;
                PORT_BSRAM: bsram_req_ack <= bsram_req;
                PORT_RV:    rv_req_ack <= rv_req;
                default: ;
                endcase
            end

            // ARAM
            if (cycle[4] && (oe_latch[1] || we_latch[1])) begin
                cmd <= we_latch[1]?CMD_Write:CMD_Read;
                if (we_latch[1]) begin
                    dq_oen <= 0;
                    dq_out <= din_latch[1];
                    SDRAM_DQM <= ~ds[1];
                end else
                    SDRAM_DQM <= 2'b00;
                a <= { 4'b0010, addr_latch[1][9:1] };  // auto precharge
			    SDRAM_BA <= 2'b10;
            end

            // read
            // ROM, WRAM, BSRAM and RV
            if (cycle[4] && oe_latch[0]) begin
                case (port[0])
                PORT_CPU:   if (cpu_port) cpu_port1 <= dq_in; else cpu_port0 <= dq_in;
                PORT_BSRAM: bsram_dout_reg <= ds[0][0] ? dq_in[7:0] : dq_in[15:8];
                PORT_RV:    rv_dout <= dq_in;
                default: ;
                endcase
            end

            // ARAM
            if (cycle[1] && oe_latch[1]) aram_dout <= dq_in;
        end
    end
end

//
// Generate cfg_now pulse after initialization delay (normally 200us)
//
reg  [14:0]   rst_cnt;
reg rst_done, rst_done_p1, cfg_busy;
  
always @(posedge clk) begin
    if (~resetn) begin
        rst_cnt  <= 15'd0;
        rst_done <= 1'b0;
        cfg_busy <= 1'b1;
    end else begin
        rst_done_p1 <= rst_done;
        cfg_now     <= rst_done & ~rst_done_p1;// Rising Edge Detect

        if (rst_cnt != FREQ / 1000 * 200 / 1000) begin      // count to 200 us
            rst_cnt  <= rst_cnt[14:0] + 15'd1;
            rst_done <= 1'b0;
            cfg_busy <= 1'b1;
        end else begin
            rst_done <= 1'b1;
            cfg_busy <= 1'b0;
        end        
    end
end

endmodule
