alanswx/Arcade-MCR2-TangFPGA/src/rtl/cmos_ram.vhd

-- -----------------------------------------------------------------------
--
-- Syntiac's generic VHDL support files.
--
-- -----------------------------------------------------------------------
-- Copyright 2005-2008 by Peter Wendrich (pwsoft@syntiac.com)
-- http://www.syntiac.com/fpga64.html
--
-- Modified April 2016 by Dar (darfpga@aol.fr) 
-- http://darfpga.blogspot.fr
--   Remove address register when writing
--
-- -----------------------------------------------------------------------
--
-- gen_rwram.vhd
--
-- -----------------------------------------------------------------------
--
-- generic ram.
--
-- -----------------------------------------------------------------------

library IEEE;
use IEEE.STD_LOGIC_1164.ALL;
use IEEE.numeric_std.ALL;

-- -----------------------------------------------------------------------

entity cmos_ram is
	generic (
		dWidth : integer := 8;
		aWidth : integer := 11
	);
	port (
		clk : in std_logic;
		we : in std_logic;
		addr : in std_logic_vector((aWidth-1) downto 0);
		d : in std_logic_vector((dWidth-1) downto 0);
		q : out std_logic_vector((dWidth-1) downto 0)
	);
end entity;

-- -----------------------------------------------------------------------

architecture rtl of cmos_ram is
	subtype addressRange is integer range 0 to ((2**aWidth)-1);
	type ramDef is array(addressRange) of std_logic_vector((dWidth-1) downto 0);
	signal ram: ramDef:= (
	X"FF",X"FF",X"FF",X"FF",X"FF",X"FF",X"FF",X"FF",X"FF",X"FF",X"FF",X"FF",X"FF",X"FF",X"FF",X"FF",  --000-00F
	X"FF",X"FF",X"FF",X"FF",X"FF",X"FF",X"FF",X"FF",X"FF",X"FF",X"FF",X"FF",X"FF",X"FF",X"FF",X"FF",  --010-01F
	X"FF",X"FF",X"FF",X"FF",X"FF",X"FF",X"FF",X"FF",X"FF",X"FF",X"FF",X"FF",X"FF",X"FF",X"FF",X"FF",  --020-02F
	X"FF",X"FF",X"FF",X"FF",X"FF",X"FF",X"FF",X"FF",X"FF",X"FF",X"FF",X"FF",X"FF",X"FF",X"FF",X"FF",  --030-03F
	X"FF",X"FF",X"FF",X"FF",X"FF",X"FF",X"FF",X"FF",X"FF",X"FF",X"FF",X"FF",X"FF",X"FF",X"FF",X"FF",  --040-04F
	X"FF",X"FF",X"FF",X"FF",X"FF",X"FF",X"FF",X"FF",X"FF",X"FF",X"FF",X"FF",X"FF",X"FF",X"FF",X"FF",  --050-05F
	X"FF",X"FF",X"FF",X"FF",X"FF",X"FF",X"FF",X"FF",X"FF",X"FF",X"FF",X"FF",X"FF",X"FF",X"FF",X"FF",  --060-06F
	X"FF",X"FF",X"FF",X"FF",X"FF",X"FF",X"FF",X"FF",X"FF",X"FF",X"FF",X"FF",X"FF",X"FF",X"FF",X"FF",  --070-07F
	X"FF",X"FF",X"FF",X"FF",X"FF",X"FF",X"FF",X"FF",X"FF",X"FF",X"FF",X"FF",X"FF",X"FF",X"FF",X"FF",  --080-08F
	X"FF",X"FF",X"FF",X"FF",X"FF",X"FF",X"FF",X"FF",X"FF",X"FF",X"FF",X"FF",X"FF",X"FF",X"FF",X"FF",  --090-09F
	X"FF",X"FF",X"FF",X"FF",X"FF",X"FF",X"FF",X"FF",X"FF",X"FF",X"FF",X"FF",X"FF",X"FF",X"FF",X"FF",  --0A0-0AF
	X"FF",X"FF",X"FF",X"FF",X"FF",X"FF",X"FF",X"FF",X"FF",X"FF",X"FF",X"FF",X"FF",X"FF",X"FF",X"FF",  --0B0-0BF
	X"FF",X"FF",X"FF",X"FF",X"FF",X"FF",X"FF",X"FF",X"FF",X"FF",X"FF",X"FF",X"FF",X"FF",X"FF",X"FF",  --0C0-0CF
	X"FF",X"FF",X"FF",X"FF",X"FF",X"FF",X"FF",X"FF",X"FF",X"FF",X"FF",X"FF",X"FF",X"FF",X"FF",X"FF",  --0D0-0DF
	X"FF",X"FF",X"FF",X"FF",X"FF",X"FF",X"FF",X"FF",X"FF",X"FF",X"FF",X"FF",X"FF",X"FF",X"FF",X"FF",  --0E0-0EF
	X"FF",X"FF",X"FF",X"FF",X"FF",X"FF",X"FF",X"FF",X"FF",X"FF",X"FF",X"FF",X"FF",X"FF",X"FF",X"FF",  --0F0-0FF

	X"FF",X"FF",X"FF",X"FF",X"FF",X"FF",X"FF",X"FF",X"FF",X"FF",X"FF",X"FF",X"FF",X"FF",X"FF",X"FF",  --100-10F
	X"FF",X"FF",X"FF",X"FF",X"FF",X"FF",X"FF",X"FF",X"FF",X"FF",X"FF",X"FF",X"FF",X"FF",X"FF",X"FF",  
	X"FF",X"FF",X"FF",X"FF",X"FF",X"FF",X"FF",X"FF",X"FF",X"FF",X"FF",X"FF",X"FF",X"FF",X"FF",X"FF",  
	X"FF",X"FF",X"FF",X"FF",X"FF",X"FF",X"FF",X"FF",X"FF",X"FF",X"FF",X"FF",X"FF",X"FF",X"FF",X"FF",  
	X"FF",X"FF",X"FF",X"FF",X"FF",X"FF",X"FF",X"FF",X"FF",X"FF",X"FF",X"FF",X"FF",X"FF",X"FF",X"FF",  
	X"FF",X"FF",X"FF",X"FF",X"FF",X"FF",X"FF",X"FF",X"FF",X"FF",X"FF",X"FF",X"FF",X"FF",X"FF",X"FF",  
	X"FF",X"FF",X"FF",X"FF",X"FF",X"FF",X"FF",X"FF",X"FF",X"FF",X"FF",X"FF",X"FF",X"FF",X"FF",X"FF",  
	X"FF",X"FF",X"FF",X"FF",X"FF",X"FF",X"FF",X"FF",X"FF",X"FF",X"FF",X"FF",X"FF",X"FF",X"FF",X"FF",  
	X"FF",X"FF",X"FF",X"FF",X"FF",X"FF",X"FF",X"FF",X"FF",X"FF",X"FF",X"FF",X"FF",X"FF",X"FF",X"FF",  
	X"FF",X"FF",X"FF",X"FF",X"FF",X"FF",X"FF",X"FF",X"FF",X"FF",X"FF",X"FF",X"FF",X"FF",X"FF",X"FF",  
	X"FF",X"FF",X"FF",X"FF",X"FF",X"FF",X"FF",X"FF",X"FF",X"FF",X"FF",X"FF",X"FF",X"FF",X"FF",X"FF",  
	X"FF",X"FF",X"FF",X"FF",X"FF",X"FF",X"FF",X"FF",X"FF",X"FF",X"FF",X"FF",X"FF",X"FF",X"FF",X"FF",  
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
--	X"FF",X"FF",X"FF",X"FF",X"FF",X"FF",X"FF",X"FF",X"FF",X"FF",X"FF",X"FF",X"FF",X"FF",X"FF",X"FF",  
--	X"FF",X"FF",X"FF",X"FF",X"FF",X"FF",X"FF",X"FF",X"FF",X"FF",X"FF",X"FF",X"FF",X"FF",X"FF",X"FF",  
--	X"FF",X"FF",X"FF",X"FF",X"FF",X"FF",X"FF",X"FF",X"FF",X"FF",X"FF",X"FF",X"FF",X"FF",X"FF",X"FF",  
--	X"FF",X"FF",X"FF",X"FF",X"FF",X"FF",X"FF",X"FF",X"FF",X"FF",X"FF",X"FF",X"FF",X"FF",X"FF",X"FF",  
--	X"FF",X"FF",X"FF",X"FF",X"FF",X"FF",X"FF",X"FF",X"FF",X"FF",X"FF",X"FF",X"FF",X"FF",X"FF",X"FF",  
--	X"FF",X"FF",X"FF",X"FF",X"FF",X"FF",X"FF",X"FF",X"FF",X"FF",X"FF",X"FF",X"FF",X"FF",X"FF",X"FF",  
--	X"FF",X"FF",X"FF",X"FF",X"FF",X"FF",X"FF",X"FF",X"FF",X"FF",X"FF",X"FF",X"FF",X"FF",X"FF",X"FF",  
--	X"FF",X"FF",X"FF",X"FF",X"FF",X"FF",X"FF",X"FF",X"FF",X"FF",X"FF",X"FF",X"FF",X"FF",X"FF",X"FF",  
--	X"FF",X"FF",X"FF",X"FF",X"FF",X"FF",X"FF",X"FF",X"FF",X"FF",X"FF",X"FF",X"FF",X"FF",X"FF",X"FF",  
--	X"FF",X"FF",X"FF",X"FF",X"FF",X"FF",X"FF",X"FF",X"FF",X"FF",X"FF",X"FF",X"FF",X"FF",X"FF",X"FF",  
--	X"FF",X"FF",X"FF",X"FF",X"FF",X"FF",X"FF",X"FF",X"FF",X"FF",X"FF",X"FF",X"FF",X"FF",X"FF",X"FF",  
--	X"FF",X"FF",X"FF",X"FF",X"FF",X"FF",X"FF",X"FF",X"FF",X"FF",X"FF",X"FF",X"FF",X"FF",X"FF",X"FF",  
--	X"FF",X"FF",X"FF",X"FF",X"FF",X"FF",X"FF",X"FF",X"FF",X"FF",X"FF",X"FF",X"FF",X"FF",X"FF",X"FF",  
--	X"FF",X"FF",X"FF",X"FF",X"FF",X"FF",X"FF",X"FF",X"FF",X"FF",X"FF",X"FF",X"FF",X"FF",X"FF",X"FF"   --FF0-FFF
);

	signal rAddrReg : std_logic_vector((aWidth-1) downto 0);
	signal qReg : std_logic_vector((dWidth-1) downto 0);
begin
-- -----------------------------------------------------------------------
-- Signals to entity interface
-- -----------------------------------------------------------------------
--	q <= qReg;

-- -----------------------------------------------------------------------
-- Memory write
-- -----------------------------------------------------------------------
	process(clk)
	begin
		if rising_edge(clk) then
			if we = '1' then
				ram(to_integer(unsigned(addr))) <= d;
			end if;
		end if;
	end process;
	
-- -----------------------------------------------------------------------
-- Memory read
-- -----------------------------------------------------------------------
process(clk)
	begin
		if rising_edge(clk) then
--			qReg <= ram(to_integer(unsigned(rAddrReg)));
--			rAddrReg <= addr;
----			qReg <= ram(to_integer(unsigned(addr)));
      q <= ram(to_integer(unsigned(addr)));
		end if;
	end process;
--q <= ram(to_integer(unsigned(addr)));
end architecture;
