alanswx/Arcade-MCR2-TangFPGA/src/rtl/gowin_pll_core80.v

// Gowin PLLA clock generator for the MCR-3 (SDRAM-sprite) 60K build.
// Input clock: 50 MHz.
//
// VCO = FCLKIN * FBDIV_SEL * MDIV_SEL / IDIV_SEL = 50 * 1 * 16 / 1 = 800 MHz
//       (must stay inside the GW5A 700-1400 MHz VCO window)
//
// This is a 60K-only fork of gowin_pll_mcr2. The core needs clk_sys (40) and
// the DDR3 framebuffer needs clk_50 (clk_g); MCR-3 additionally needs an SDRAM
// clock that is SYNCHRONOUS to the 40 MHz core (2x = 80 MHz, one VCO) so the
// sprite read (sp_addr -> sp_q) is deterministic and needs no async CDC. 80 MHz
// is not an integer divide of the 1000 MHz VCO gowin_pll_mcr2 uses, so we drop
// to VCO=800 (a common multiple of 40/50/80) here. The 60K has no use for the
// 125 MHz TMDS clock (HDMI is the DDR3 framebuffer), so that output is dropped.
// The shared gowin_pll_mcr2 (VCO=1000, 125 MHz for the 25K's dvi_tx) is
// untouched.
//
// Output clocks:
// - clk_sys:   40 MHz (VCO/ODIV1 = 800/20) - core system clock (20 MHz pix ena)
// - clk_sdram: 80 MHz (VCO/ODIV0 = 800/10) - SDRAM controller, 2x clk_sys,
//              phase-locked (same VCO) -> synchronous 1:2 crossing to the core
// - clk_50:    50 MHz (VCO/ODIV2 = 800/16) - global-routed 50 MHz for the DDR3
//              controller's clk_g (PR1014: must be PLL-fed, not the raw pad)
module gowin_pll_core80 (
    input  clkin,
    output clk_sys,
    output clk_sdram,
    output clk_sdram_ph,  // 80 MHz, 90 deg LAG - SDRAM_CLK pin forwarder only
    output clk_50,
    output lock
);

wire clkout4_o;
wire clkout5_o;
wire clkout6_o;
wire clkfbout_o;
wire [7:0] mdrdo_o;
wire gw_gnd = 1'b0;

PLLA PLLA_inst (
    .LOCK(lock),
    .CLKOUT0(clk_sdram), // 80 MHz
    .CLKOUT1(clk_sys),   // 40 MHz
    .CLKOUT2(clk_50),    // 50 MHz
    .CLKOUT3(clk_sdram_ph),  // 80 MHz +90deg for the SDRAM pin clock
    .CLKOUT4(clkout4_o),
    .CLKOUT5(clkout5_o),
    .CLKOUT6(clkout6_o),
    .CLKFBOUT(clkfbout_o),
    .MDRDO(mdrdo_o),
    .CLKIN(clkin),
    .CLKFB(gw_gnd),
    .RESET(gw_gnd),
    .PLLPWD(gw_gnd),
    .RESET_I(gw_gnd),
    .RESET_O(gw_gnd),
    .PSSEL({gw_gnd,gw_gnd,gw_gnd}),
    .PSDIR(gw_gnd),
    .PSPULSE(gw_gnd),
    .SSCPOL(gw_gnd),
    .SSCON(gw_gnd),
    .SSCMDSEL({gw_gnd,gw_gnd,gw_gnd,gw_gnd,gw_gnd,gw_gnd,gw_gnd}),
    .SSCMDSEL_FRAC({gw_gnd,gw_gnd,gw_gnd}),
    .MDCLK(gw_gnd),
    .MDOPC({gw_gnd,gw_gnd}),
    .MDAINC(gw_gnd),
    .MDWDI({gw_gnd,gw_gnd,gw_gnd,gw_gnd,gw_gnd,gw_gnd,gw_gnd,gw_gnd})
);

defparam PLLA_inst.FCLKIN = "50";
defparam PLLA_inst.IDIV_SEL = 1;
defparam PLLA_inst.FBDIV_SEL = 1;
defparam PLLA_inst.CLKFB_SEL = "INTERNAL";
defparam PLLA_inst.ODIV0_SEL = 10;   // clk_sdram = 800/10 = 80 MHz
defparam PLLA_inst.ODIV0_FRAC_SEL = 0;
defparam PLLA_inst.ODIV1_SEL = 20;   // clk_sys   = 800/20 = 40 MHz
defparam PLLA_inst.ODIV2_SEL = 16;   // clk_50    = 800/16 = 50 MHz
defparam PLLA_inst.ODIV3_SEL = 10;   // 800/10 = 80 MHz, same as clk_sdram
defparam PLLA_inst.ODIV4_SEL = 8;
defparam PLLA_inst.ODIV5_SEL = 8;
defparam PLLA_inst.ODIV6_SEL = 8;
defparam PLLA_inst.MDIV_SEL = 16;    // VCO = 50 * 16 = 800 MHz
defparam PLLA_inst.MDIV_FRAC_SEL = 0;
defparam PLLA_inst.CLKOUT0_EN = "TRUE";
defparam PLLA_inst.CLKOUT1_EN = "TRUE";
defparam PLLA_inst.CLKOUT2_EN = "TRUE";
defparam PLLA_inst.CLKOUT3_EN = "TRUE";   // 90-deg SDRAM pin clock
defparam PLLA_inst.CLKOUT4_EN = "FALSE";
defparam PLLA_inst.CLKOUT5_EN = "FALSE";
defparam PLLA_inst.CLKOUT6_EN = "FALSE";
defparam PLLA_inst.CLKOUT0_DT_DIR = 1'b1;
defparam PLLA_inst.CLKOUT1_DT_DIR = 1'b1;
defparam PLLA_inst.CLKOUT2_DT_DIR = 1'b1;
defparam PLLA_inst.CLKOUT3_DT_DIR = 1'b1;
defparam PLLA_inst.CLK0_IN_SEL = 1'b0;
defparam PLLA_inst.CLK0_OUT_SEL = 1'b0;
defparam PLLA_inst.CLK1_IN_SEL = 1'b0;
defparam PLLA_inst.CLK1_OUT_SEL = 1'b0;
defparam PLLA_inst.CLK2_IN_SEL = 1'b0;
defparam PLLA_inst.CLK2_OUT_SEL = 1'b0;
defparam PLLA_inst.CLK3_IN_SEL = 1'b0;
defparam PLLA_inst.CLK3_OUT_SEL = 1'b0;
defparam PLLA_inst.CLK4_IN_SEL = 2'b00;
defparam PLLA_inst.CLK4_OUT_SEL = 1'b0;
defparam PLLA_inst.CLK5_IN_SEL = 1'b0;
defparam PLLA_inst.CLK5_OUT_SEL = 1'b0;
defparam PLLA_inst.CLK6_IN_SEL = 1'b0;
defparam PLLA_inst.CLK6_OUT_SEL = 1'b0;
defparam PLLA_inst.CLKOUT0_PE_COARSE = 0;
defparam PLLA_inst.CLKOUT0_PE_FINE = 0;
defparam PLLA_inst.CLKOUT1_PE_COARSE = 0;
defparam PLLA_inst.CLKOUT1_PE_FINE = 0;
defparam PLLA_inst.CLKOUT2_PE_COARSE = 0;
defparam PLLA_inst.CLKOUT2_PE_FINE = 0;
// Phase: PE in VCO cycles (1.25ns @800MHz); ODIV3=10 -> period=10 VCO.
// 225 deg = 6.25 VCO (6 coarse + 2/8 fine) - the discipline every nand2mario
// SDRAM design uses (snestang: assign O_sdram_clk = fclk_p @225deg), and
// PROVEN on this board 2026-07-24: pure-upstream sdram_gw + 225deg retains
// data with 0 errors at 8+ minutes of age, where 0 deg lost everything in
// ~30-100s and 90 deg was never validated end-to-end.
defparam PLLA_inst.CLKOUT3_PE_COARSE = 6;
defparam PLLA_inst.CLKOUT3_PE_FINE = 2;
defparam PLLA_inst.CLKOUT4_PE_COARSE = 0;
defparam PLLA_inst.CLKOUT4_PE_FINE = 0;
defparam PLLA_inst.CLKOUT5_PE_COARSE = 0;
defparam PLLA_inst.CLKOUT5_PE_FINE = 0;
defparam PLLA_inst.CLKOUT6_PE_COARSE = 0;
defparam PLLA_inst.CLKOUT6_PE_FINE = 0;
defparam PLLA_inst.DE0_EN = "FALSE";
defparam PLLA_inst.DE1_EN = "FALSE";
defparam PLLA_inst.DE2_EN = "FALSE";
defparam PLLA_inst.DE3_EN = "FALSE";
defparam PLLA_inst.DE4_EN = "FALSE";
defparam PLLA_inst.DE5_EN = "FALSE";
defparam PLLA_inst.DE6_EN = "FALSE";
defparam PLLA_inst.DYN_DPA_EN = "FALSE";
defparam PLLA_inst.DYN_PE0_SEL = "FALSE";
defparam PLLA_inst.DYN_PE1_SEL = "FALSE";
defparam PLLA_inst.DYN_PE2_SEL = "FALSE";
defparam PLLA_inst.DYN_PE3_SEL = "FALSE";
defparam PLLA_inst.DYN_PE4_SEL = "FALSE";
defparam PLLA_inst.DYN_PE5_SEL = "FALSE";
defparam PLLA_inst.DYN_PE6_SEL = "FALSE";
defparam PLLA_inst.RESET_I_EN = "FALSE";
defparam PLLA_inst.RESET_O_EN = "FALSE";
defparam PLLA_inst.ICP_SEL = 6'bXXXXXX;
defparam PLLA_inst.LPF_RES = 3'bXXX;
defparam PLLA_inst.LPF_CAP = 2'b00;
defparam PLLA_inst.SSC_EN = "FALSE";
defparam PLLA_inst.CLKOUT0_DT_STEP = 0;
defparam PLLA_inst.CLKOUT1_DT_STEP = 0;
defparam PLLA_inst.CLKOUT2_DT_STEP = 0;
defparam PLLA_inst.CLKOUT3_DT_STEP = 0;

endmodule
